openenergymonitor/STM32/Hardware/spice_models/current path1.png

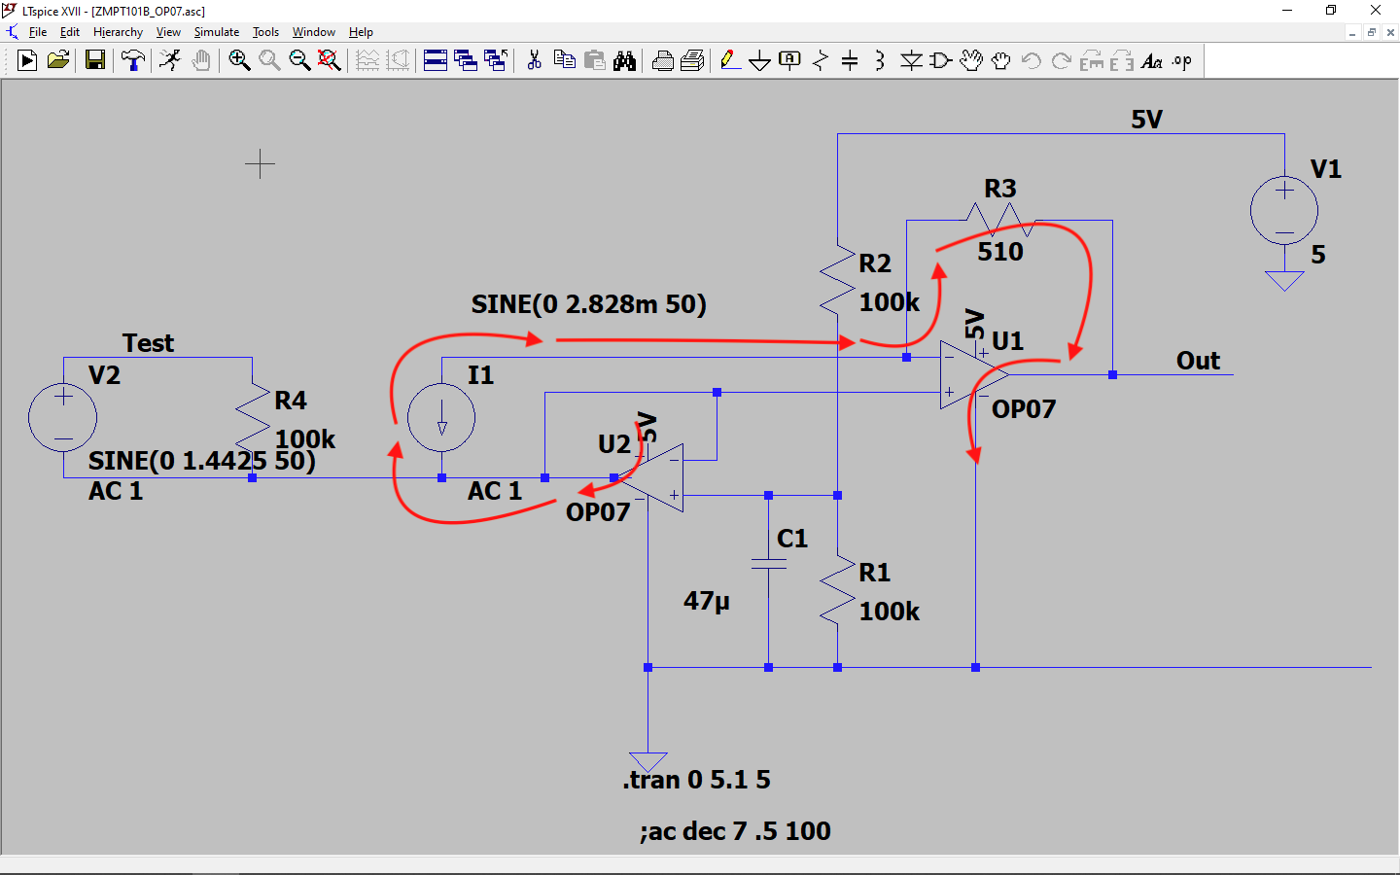
Hardware/spice_models/current path1.png
