openenergymonitor/STM32/Hardware/stm32-pi_basic/5/board.png

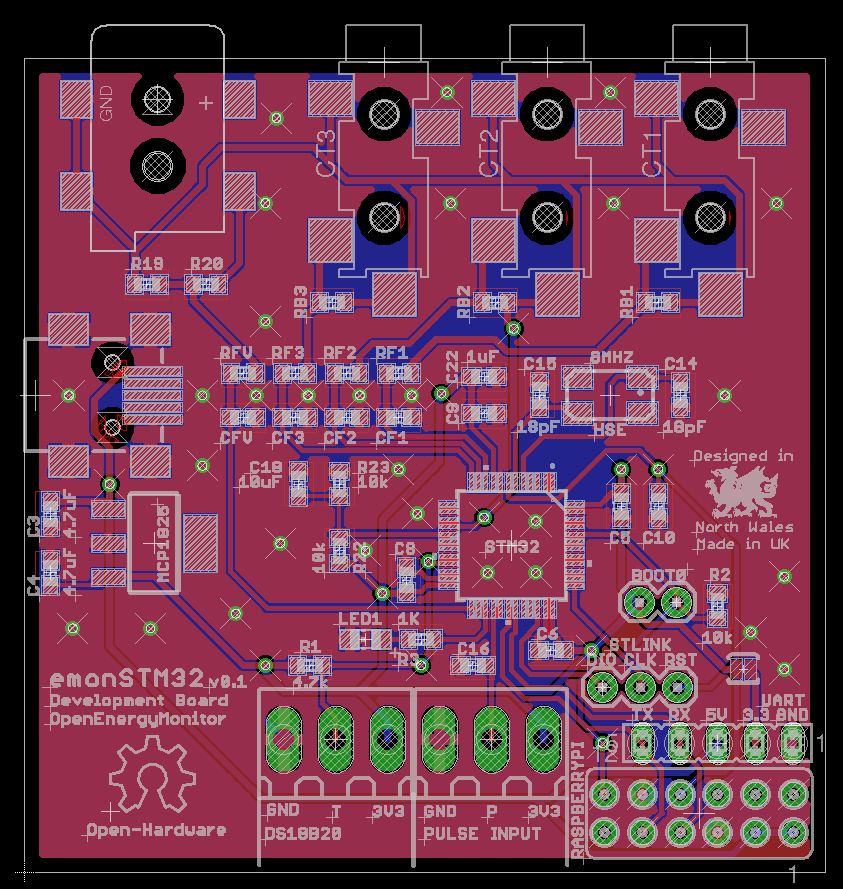
Hardware/stm32-pi_basic/5/board.png
