openenergymonitor/STM32/Hardware/stm32-pi_full/_datasheets/usw25w2a_04.jpg

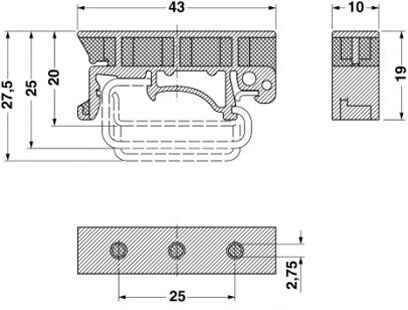
Hardware/stm32-pi_full/_datasheets/usw25w2a_04.jpg
