openenergymonitor/STM32/Hardware/stm32-pi_full/_datasheets/voltage stm32 watt hour meter.png

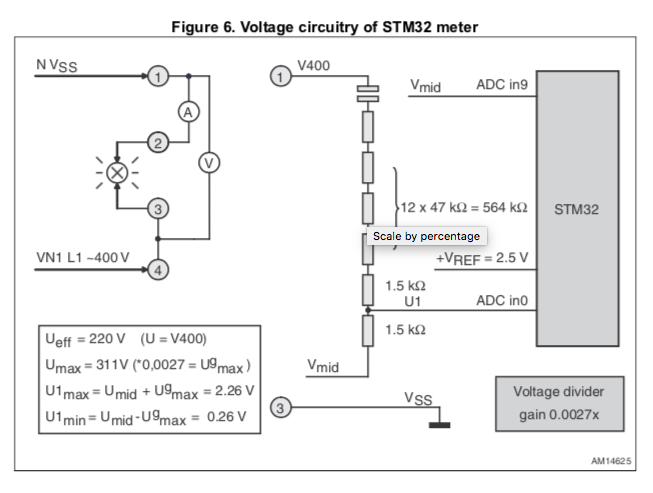
Hardware/stm32-pi_full/_datasheets/voltage stm32 watt hour meter.png
