openenergymonitor/STM32/Hardware/stm32-pi_full/_images/tp-link router.jpg

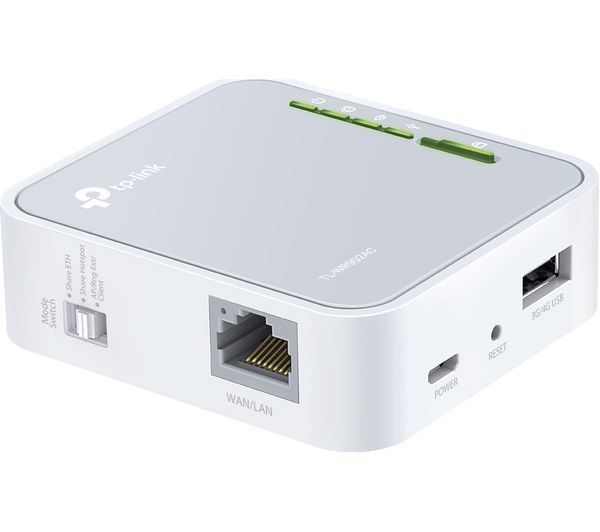
Hardware/stm32-pi_full/_images/tp-link router.jpg
