openenergymonitor/STM32/Hardware/stm32-pi_full/_images/v0.5/2019-07-29 11.01.41.jpg

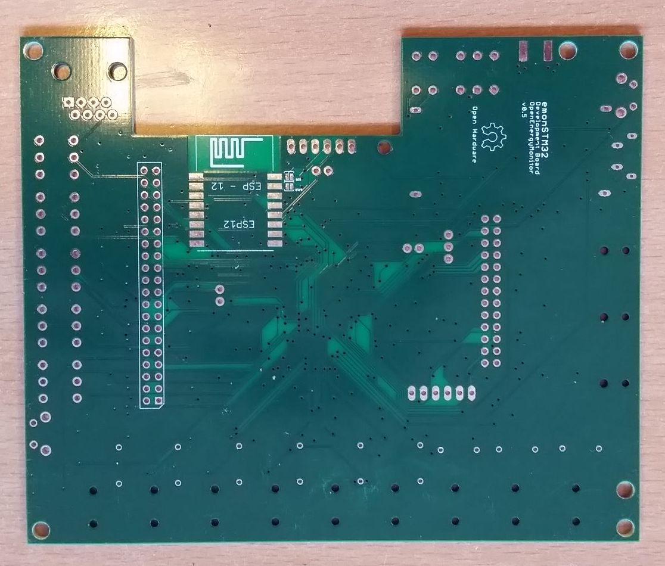
Hardware/stm32-pi_full/_images/v0.5/2019-07-29 11.01.41.jpg
