openenergymonitor/STM32/Hardware/stm32-pi_full/_images/v0.5/2019-08-09 16.36.07.jpg

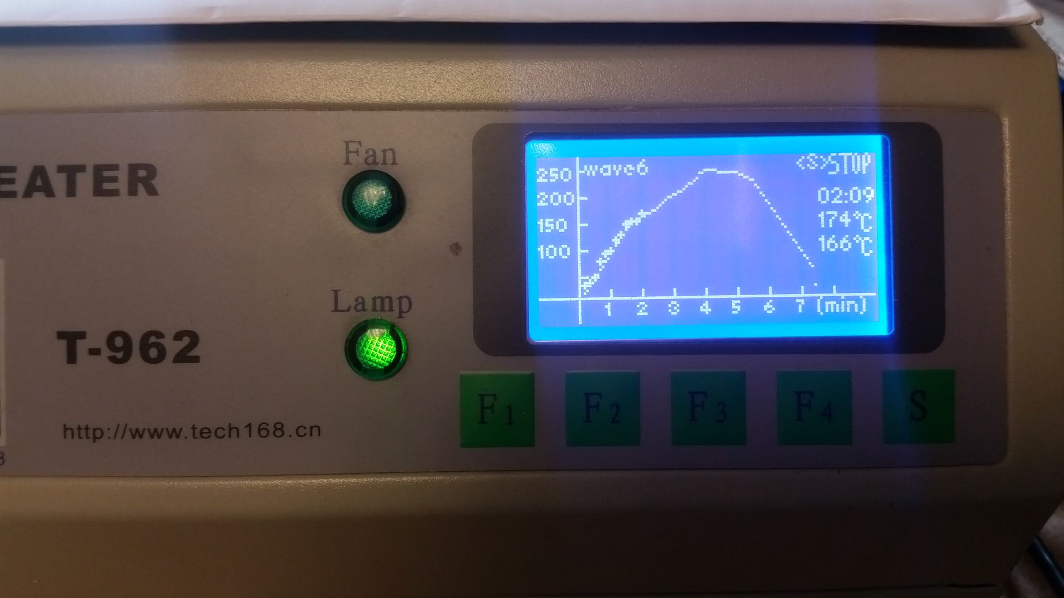
Hardware/stm32-pi_full/_images/v0.5/2019-08-09 16.36.07.jpg
