openenergymonitor/STM32/Hardware/stm32-pi_full/_images/v0.5/2019-08-09 17.46.59.jpg

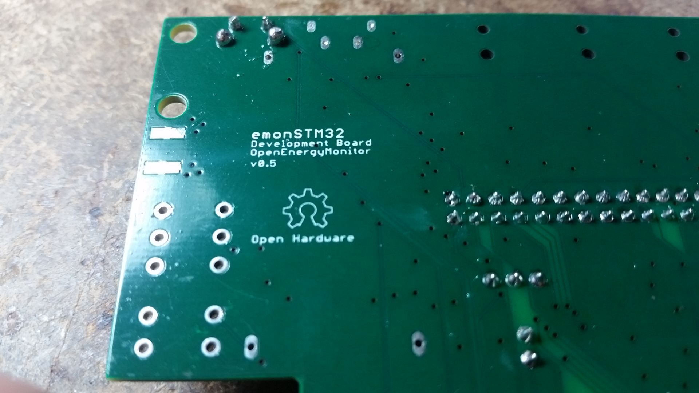
Hardware/stm32-pi_full/_images/v0.5/2019-08-09 17.46.59.jpg
