openenergymonitor/STM32/Hardware/stm32-pi_full/_images/v0.5/v0.5 2019-08-30 15.09.01.jpg

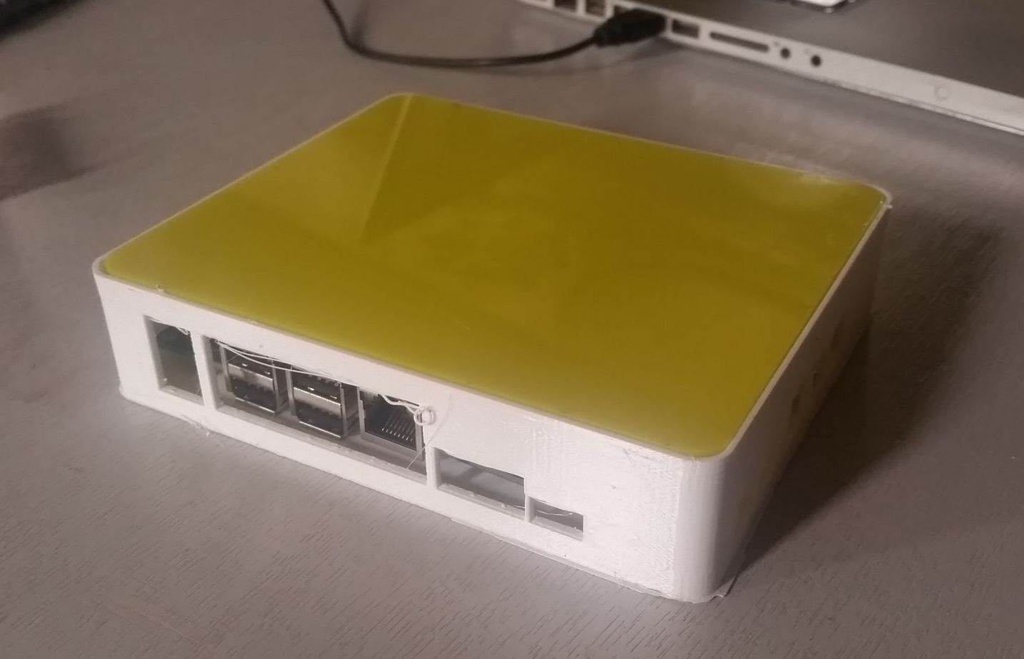
Hardware/stm32-pi_full/_images/v0.5/v0.5 2019-08-30 15.09.01.jpg
