openenergymonitor/STM32/Hardware/stm32-pi_full/_images/v0.6 Sept 2019/v0.6 top pcb.png

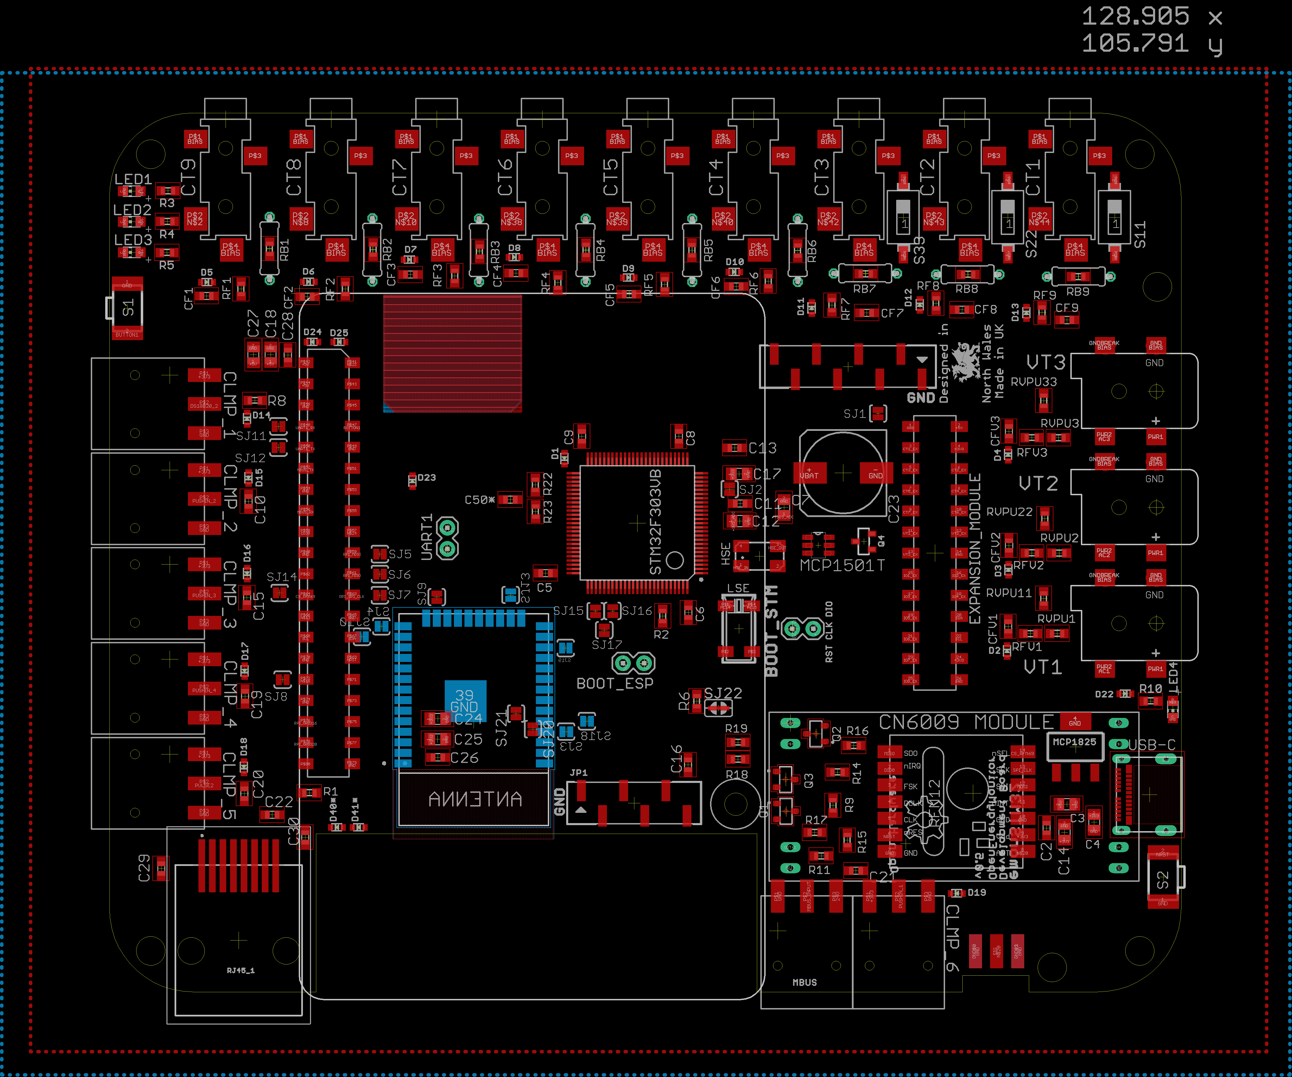
Hardware/stm32-pi_full/_images/v0.6 Sept 2019/v0.6 top pcb.png
