openenergymonitor/STM32/images/cad enclosure1.png

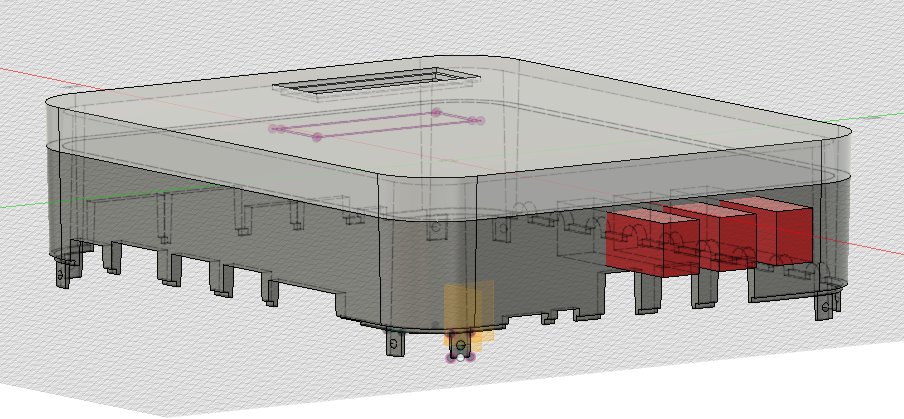
images/cad enclosure1.png
