openenergymonitor/STM32/images/emon3ct_pins.jpg

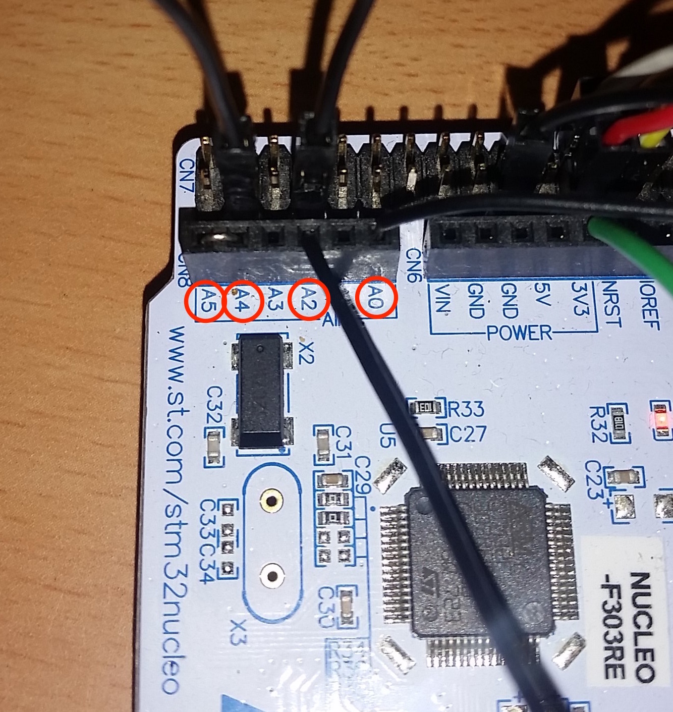
images/emon3ct_pins.jpg
