openenergymonitor/STM32/images/lowpassq.JPG

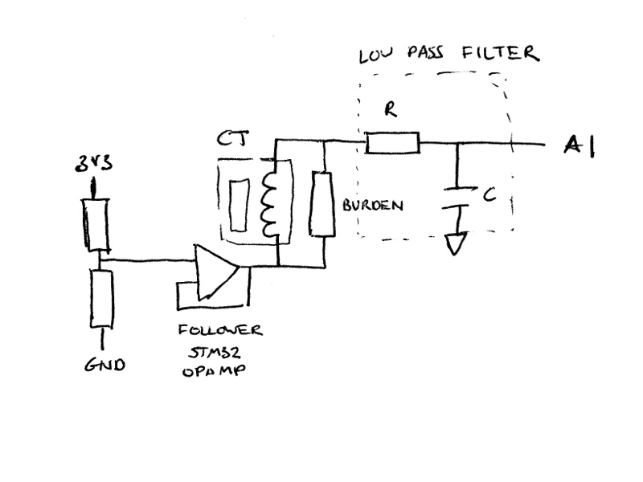
images/lowpassq.JPG
