openenergymonitor/STM32/images/stm32 orcad files to eaglecad/9.jpeg

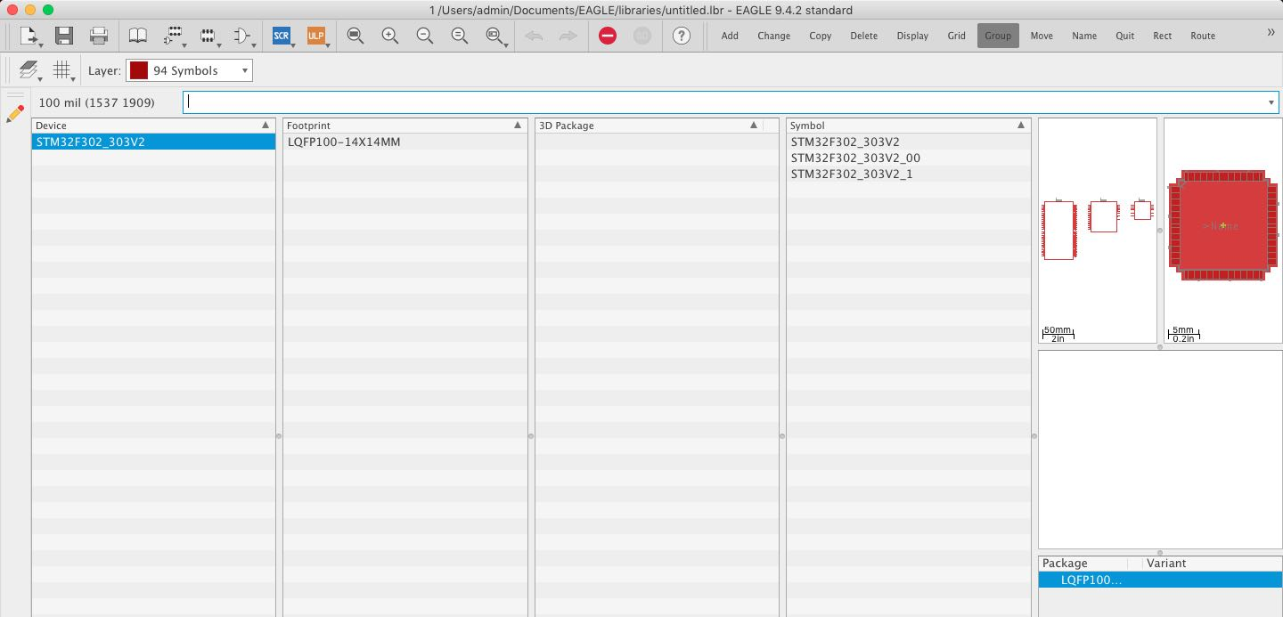
images/stm32 orcad files to eaglecad/9.jpeg
