openenergymonitor/STM32/images/stm32f303cb/stm32f303cbt6_uarts.png

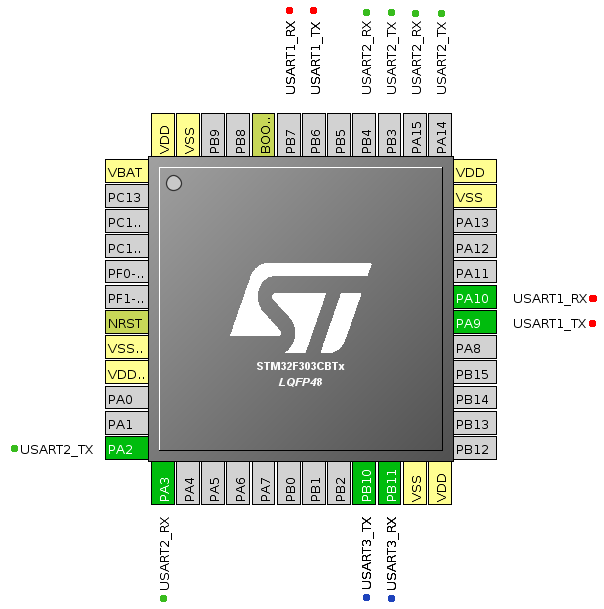
images/stm32f303cb/stm32f303cbt6_uarts.png
