openenergymonitor/STM32/images/TIM8.png

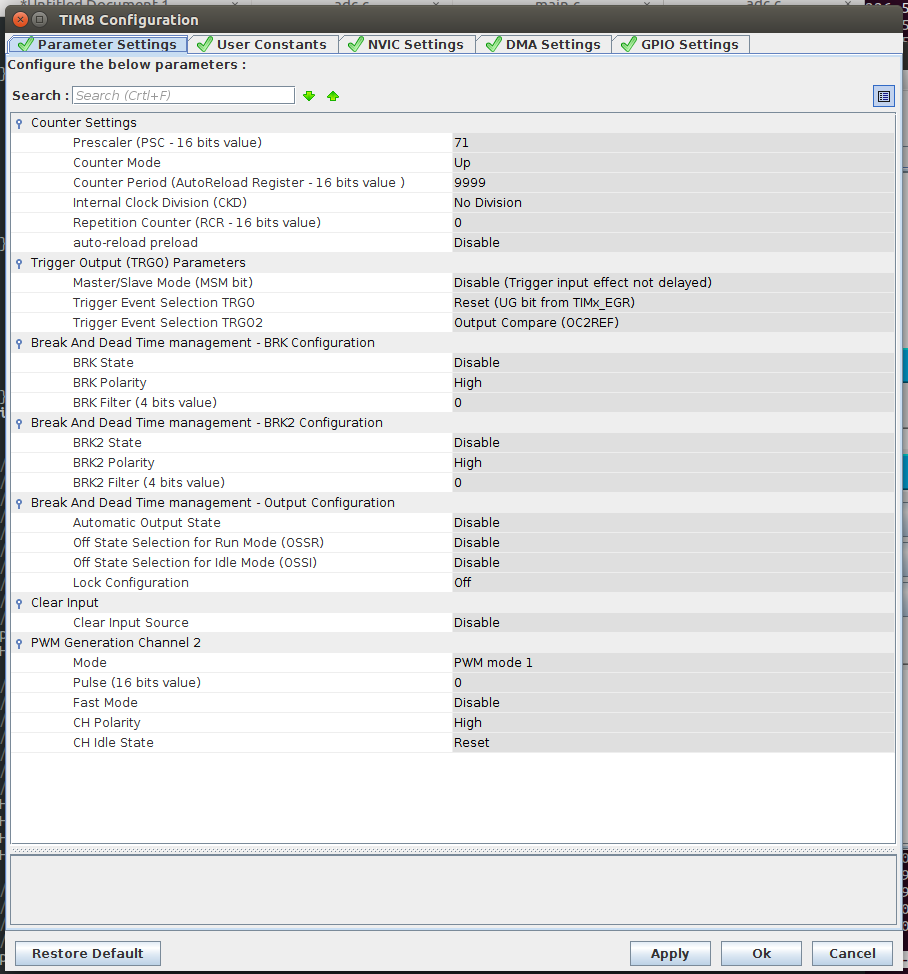
images/TIM8.png
