openenergymonitor/STM32/images/txshield_3.3V_mod.jpg

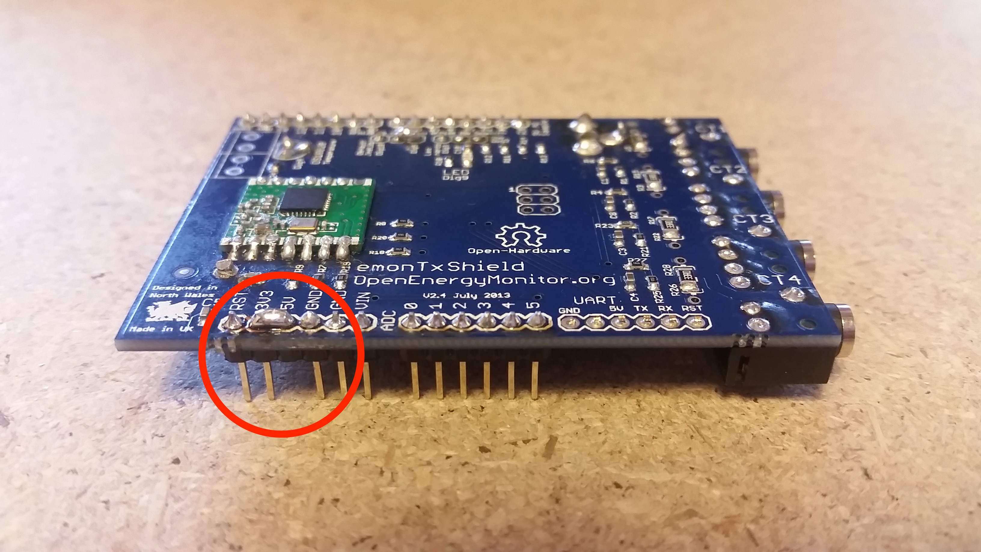
images/txshield_3.3V_mod.jpg
