openenergymonitor/STM32/images/v0.7 routing screeshots/cts vts gnd pwr.png

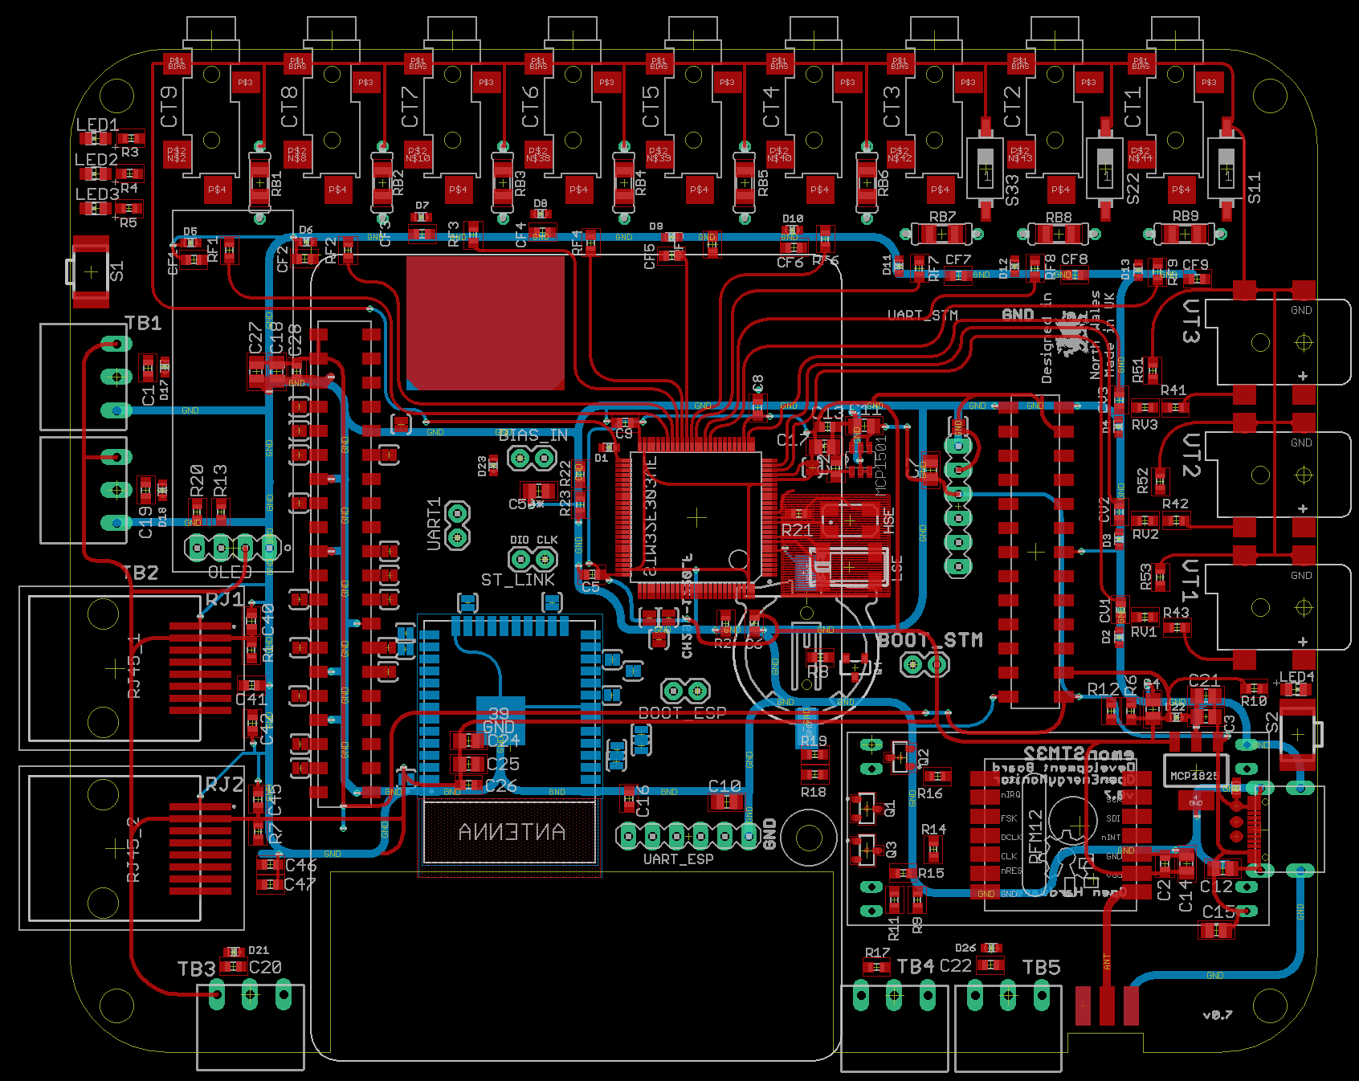
images/v0.7 routing screeshots/cts vts gnd pwr.png
