openenergymonitor/STM32/literature/3phase_amp_volt_nano.jpg

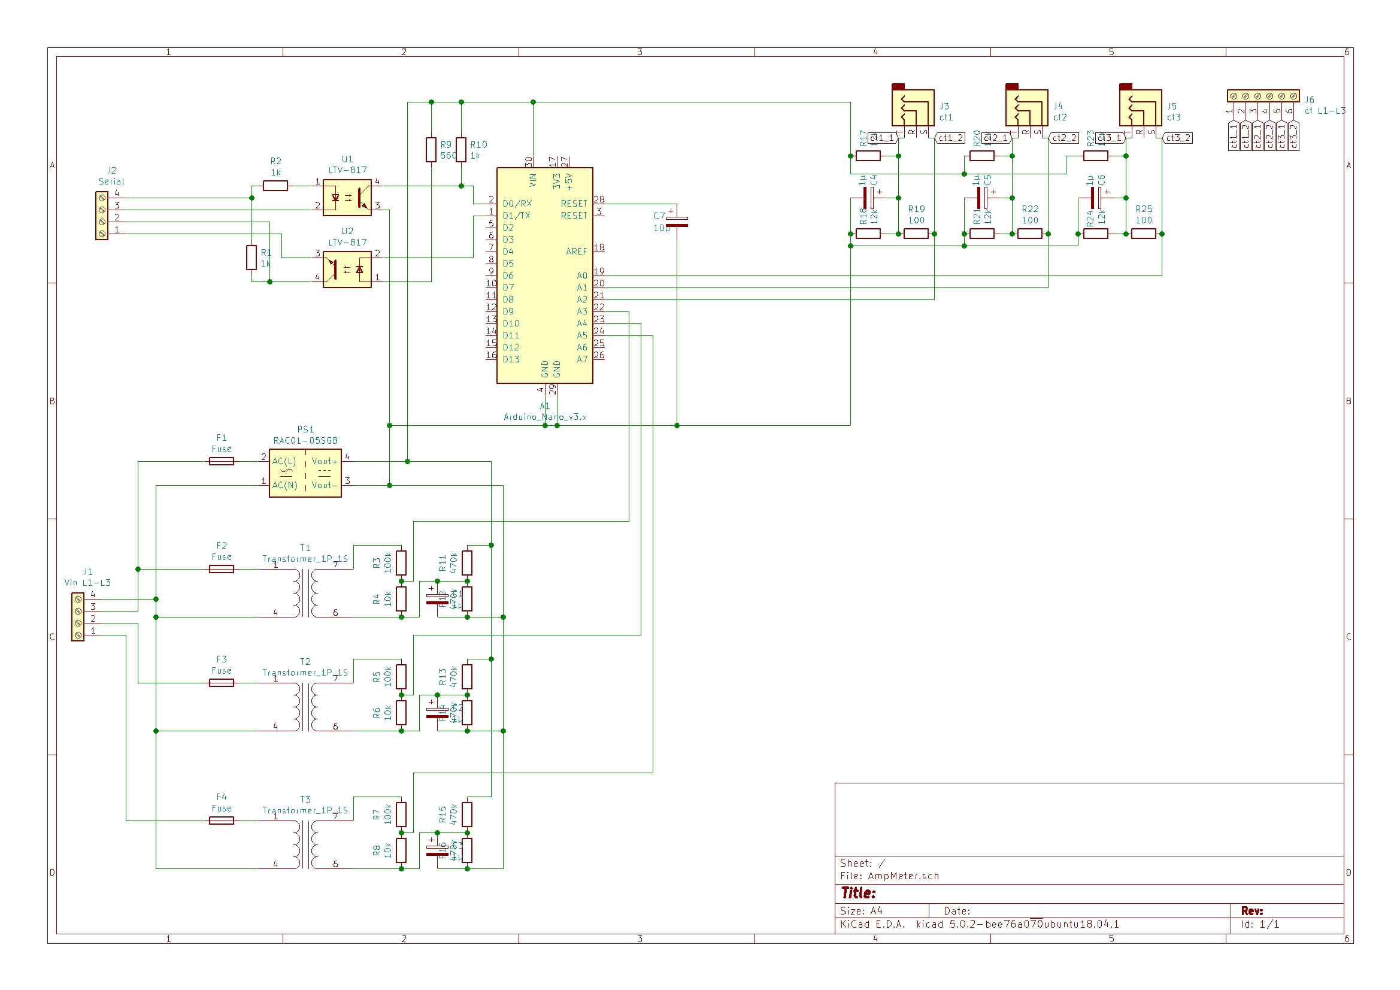
literature/3phase_amp_volt_nano.jpg
