openenergymonitor/STM32/Software/DAC_F303K8/3-phase generator/working1.jpg

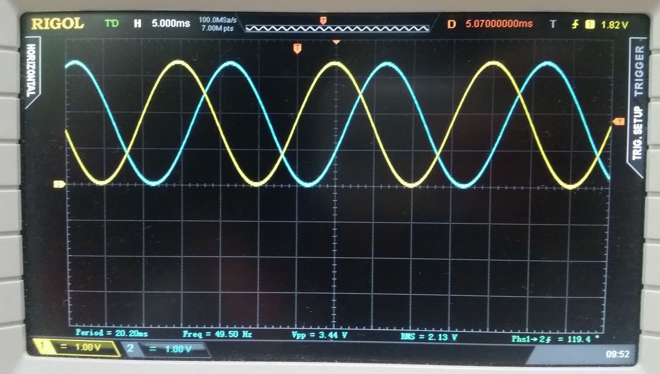
Software/DAC_F303K8/3-phase generator/working1.jpg
