openenergymonitor/STM32/Software/DAC_F303K8/3-phase generator/working2.jpg

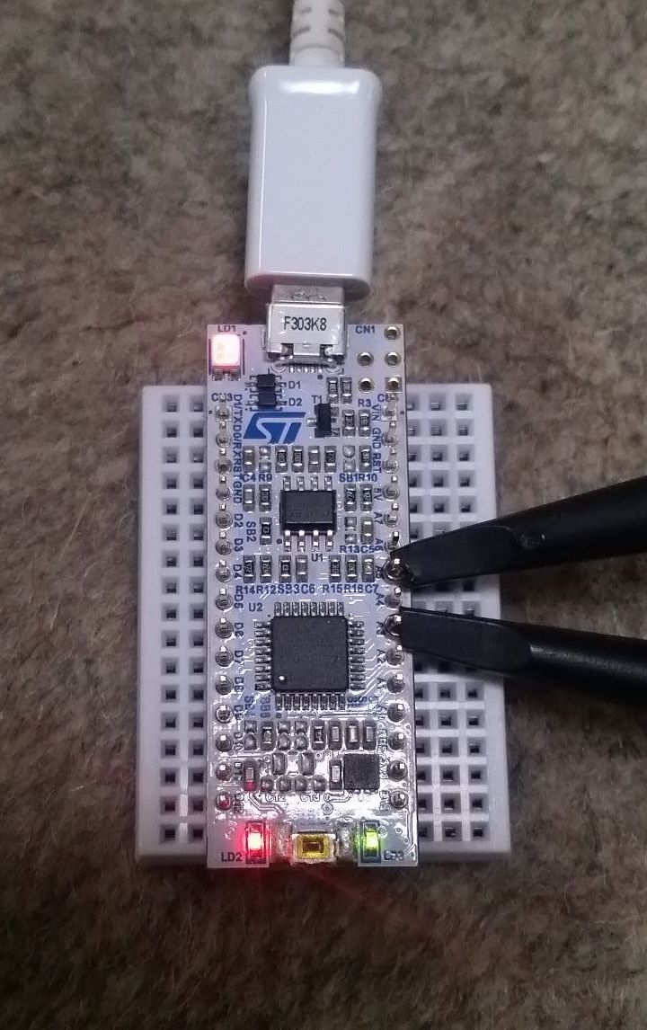
Software/DAC_F303K8/3-phase generator/working2.jpg
