openenergymonitor/STM32/Software/Emon3CT/fritzing diagram draft.png

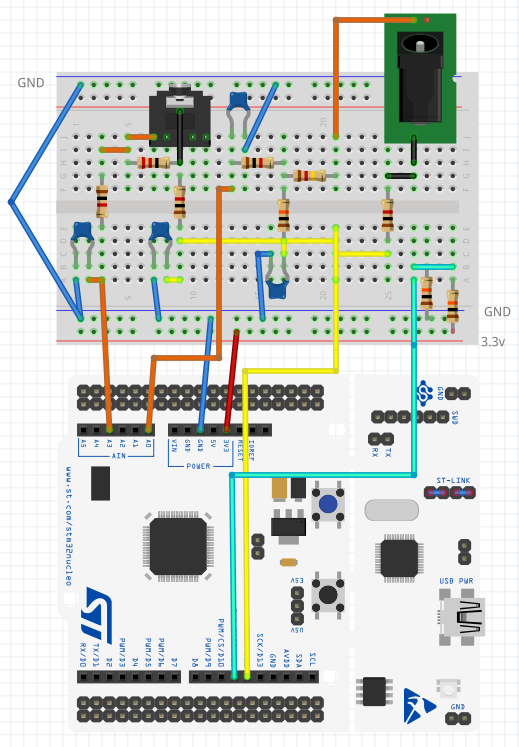
Software/Emon3CT/fritzing diagram draft.png
