openenergymonitor/STM32/images/rfm69_images/emon3ct_rfm69_wiring.jpg

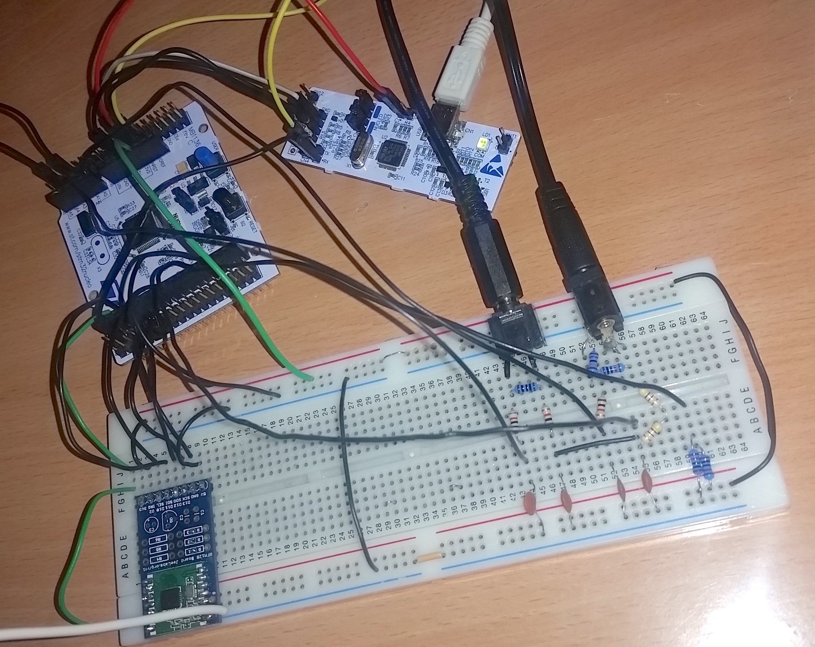
images/rfm69_images/emon3ct_rfm69_wiring.jpg
