openenergymonitor/STM32/docs/tests/1_diagram.png

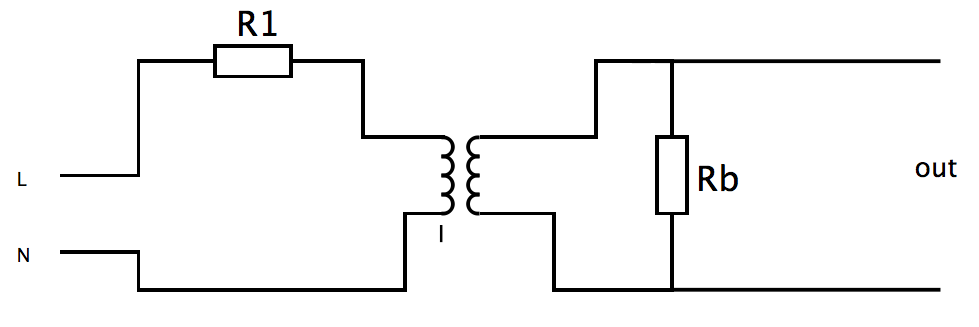
docs/tests/1_diagram.png
