openenergymonitor/STM32/docs/tests/u.i. test 29-9-2020.jpg

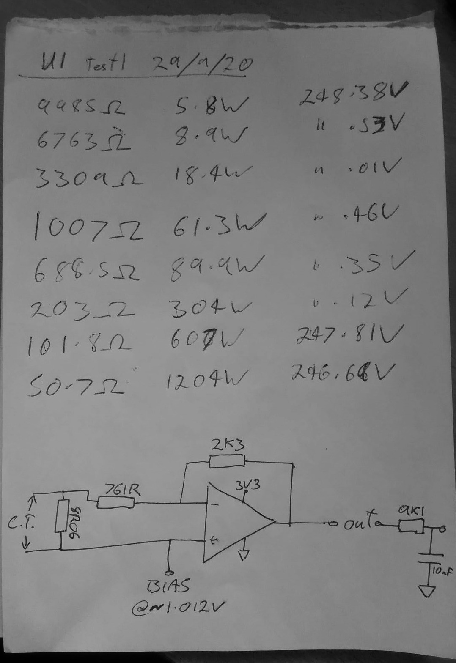
docs/tests/u.i. test 29-9-2020.jpg
