openenergymonitor/STM32/Hardware/stm32-pi_basic/4/stm32hw03.brd

## EAGLE design Hardware/stm32-pi_basic/4/stm32hw03.brd (2018-11-28)

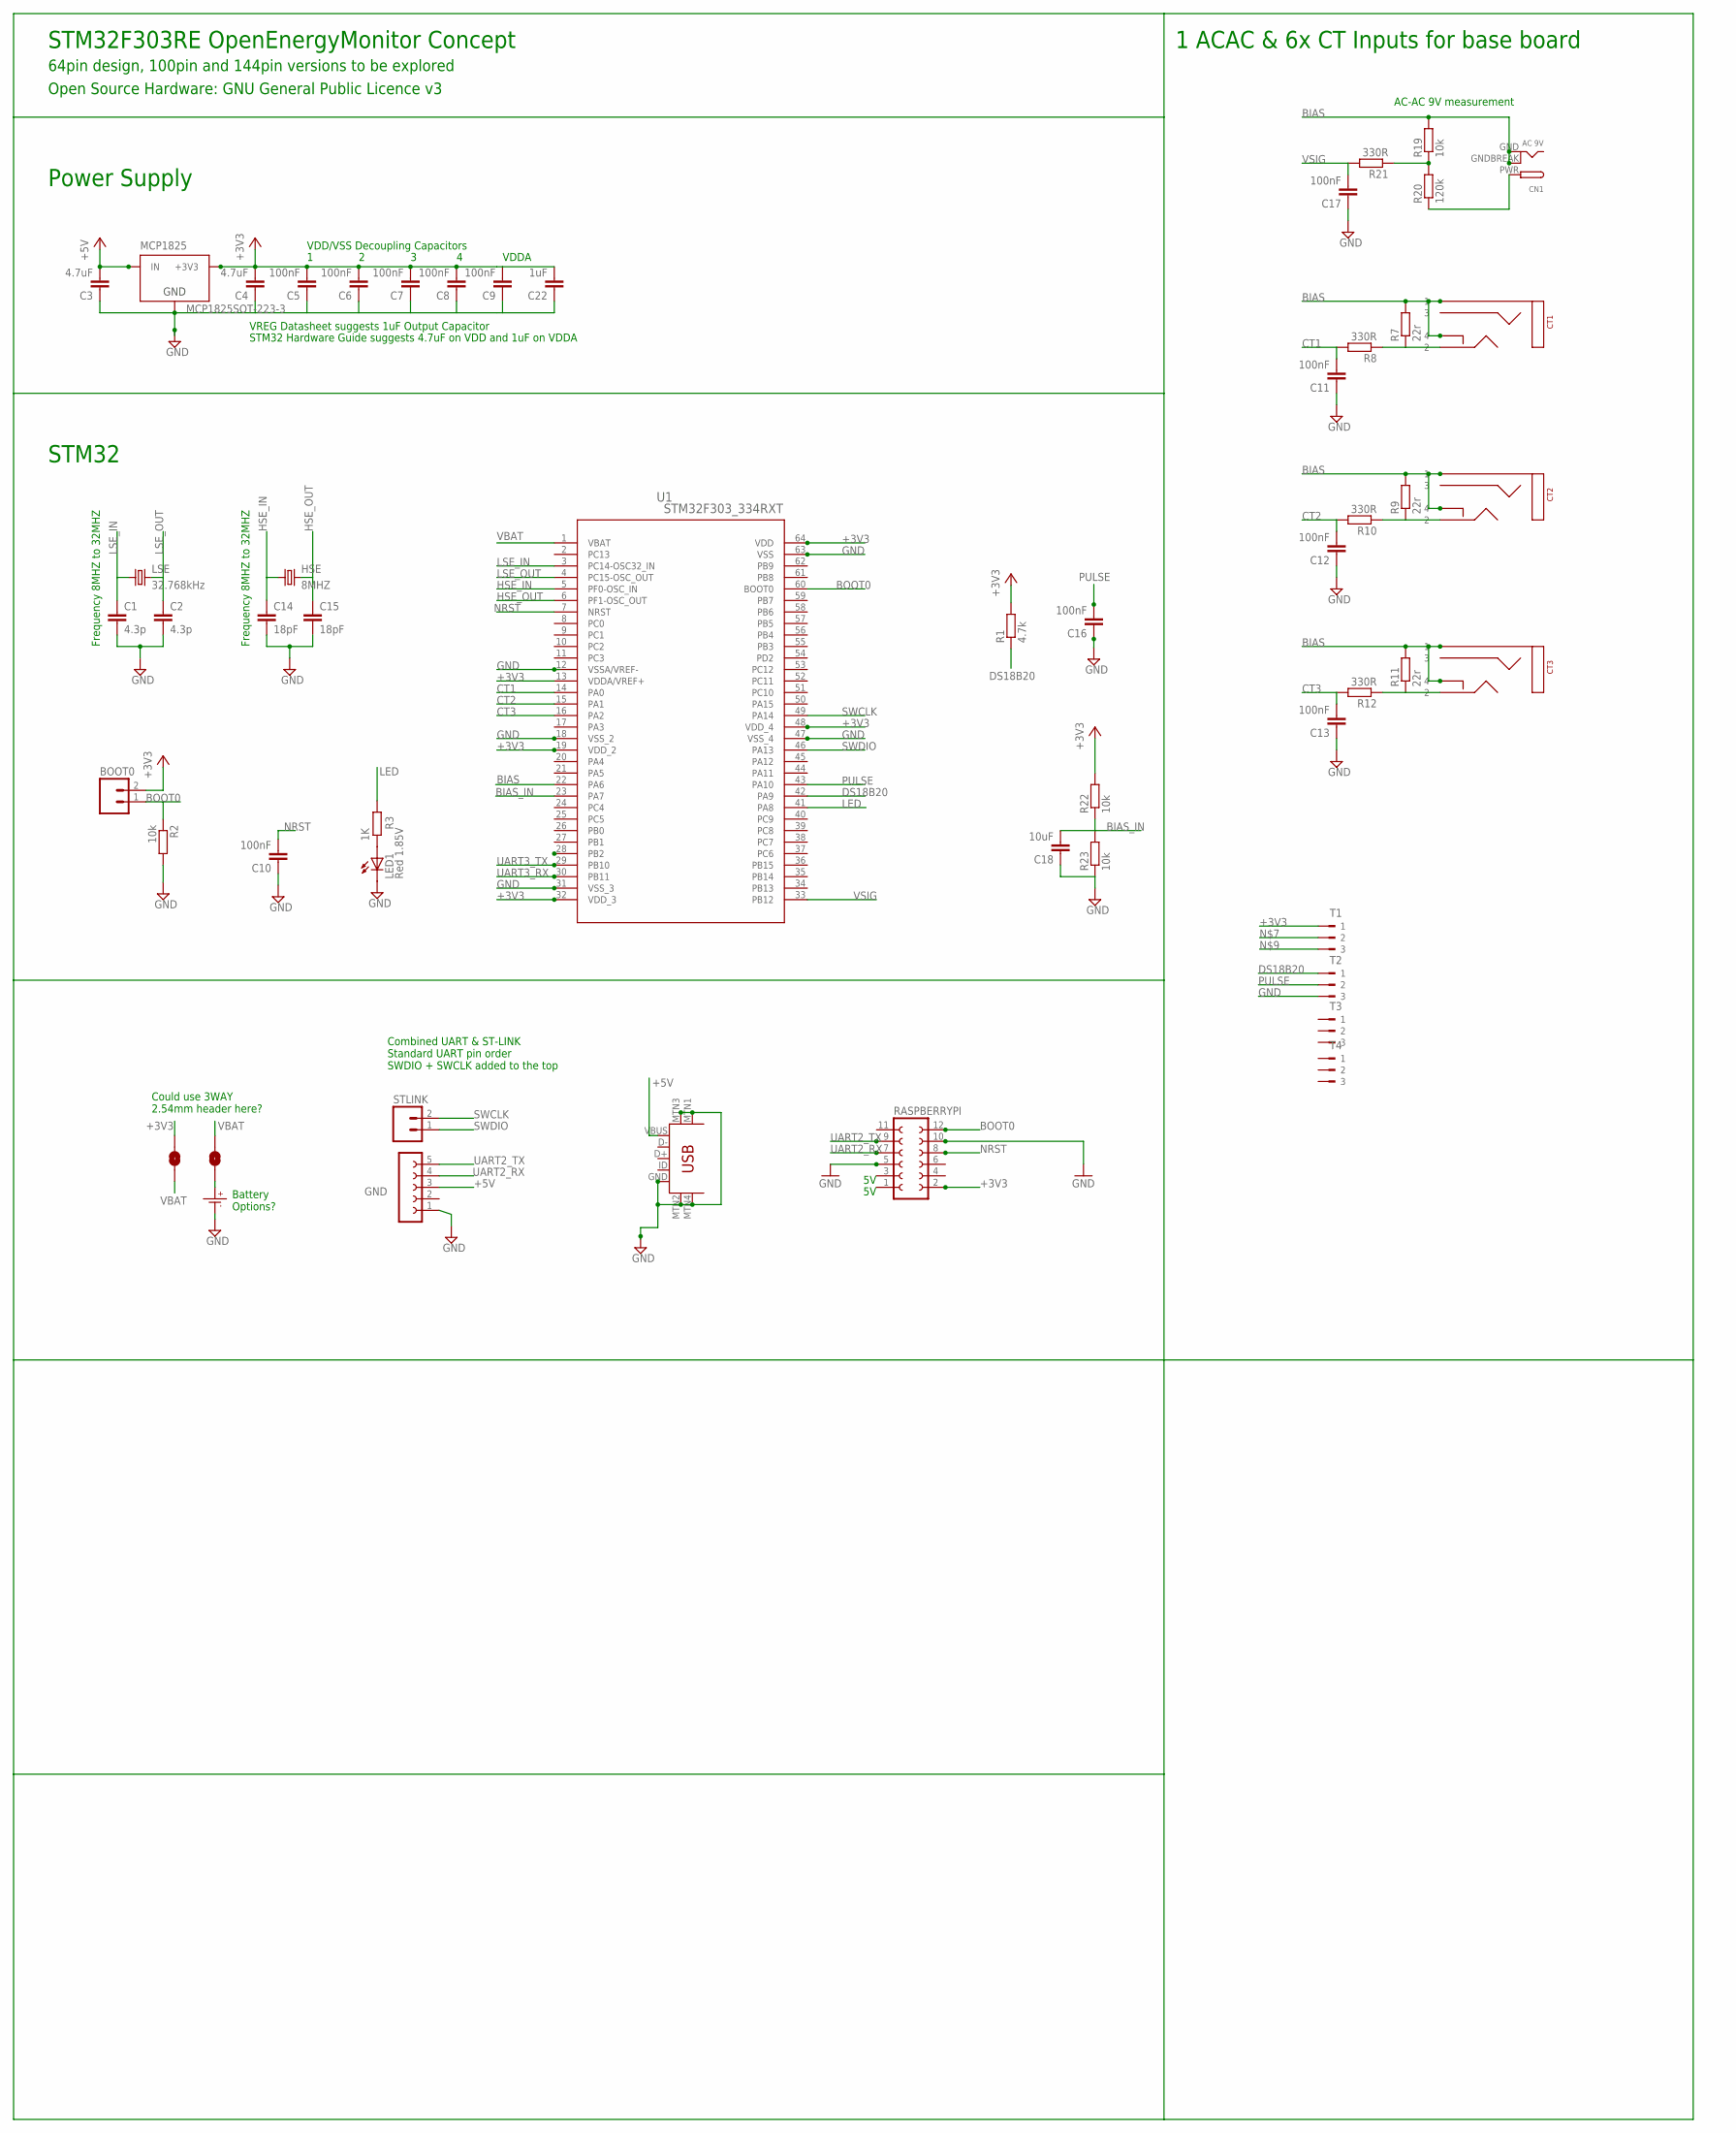
[picture p140: schematic stm32hw03.sch]

Parts:
3V3: SOLDERJUMPERNO; SJ_2S-NO
BATTERY: SOLDERJUMPERNO; SJ_2S-NO
BOOT0: M02PTH; 1X02
C1, C2: 4.3p; C0603
C3, C4: 4.7uF; C0603
C5, C6, C7, C8, C9, C10, C11, C12, C13, C16, C17: 100nF; C0603
C14, C15: 18pF; C0603
C18: 10uF; C0603
C22: 1uF; C0603
CN1: AC 9V; DCJACK_2MM_PTH
CR1220: CR1220SMD; MPN Harwin S8411-45R
CT1, CT2, CT3: STEREO_SMD; STEREO_SMT
GND: UART; FE05-1
HSE: 8MHZ; CTS406
LED1: Red 1.85V; CHIP-LED0805
LSE: 32.768kHz; MC-306
MCP1825: MCP1825SOT-223-3; SOT-223
R1: 4.7k; R0603
R2, R19, R22, R23: 10k; R0603
R3: 1K; R0603
R7, R9, R11: 22r; R0603
R8, R10, R12, R21: 330R; R0603
R20: 120k; R0603
RASPBERRYPI: FE06-2
STLINK: M02PTH; 1X02
T1, T2, T3, T4: 180-3
U1: STM32F303_334RXT; LQFP64-10X10MM
U$10: USB-MINIB-5PIN; USB-MINIB-CISECO

Connections:
+3V3: 3V3.1, BOOT0.2, C4.2, C5.2, C6.2, C7.2, C8.2, C9.2, C22.2, MCP1825.3 (+3V3), R1.2, R22.2, RASPBERRYPI.2, T1.1, U1.13 (VDDA/VREF+), U1.19 (VDD_2), U1.32 (VDD_3), U1.48 (VDD_4), U1.64 (VDD)
+5V: C3.2, GND.3, MCP1825.1 (IN), U$10.VBUS
AC: CN1.PWR, R20.1
ADC0: R19.1, R20.2, R21.1
BIAS: CN1.GND, CN1.GNDBREAK, CT1.P$1 (1), CT1.P$4 (4), CT2.P$1 (1), CT2.P$4 (4), CT3.P$1 (1), CT3.P$4 (4), R7.2, R9.2, R11.2, R19.2, U1.22 (PA6)
BIAS_IN: C18.2, R22.1, R23.2, U1.23 (PA7)
BOOT0: BOOT0.1, R2.1, RASPBERRYPI.12, U1.60 (BOOT0)
CT1: C11.2, R8.2, U1.14 (PA0)
CT2: C12.2, R10.2, U1.15 (PA1)
CT3: C13.2, R12.2, U1.16 (PA2)
DS18B20: R1.1, T2.1, U1.42 (PA9)
GND: C1.2, C2.2, C3.1, C4.1, C5.1, C6.1, C7.1, C8.1, C9.1, C10.1, C11.1, C12.1, C13.1, C14.2, C15.2, C16.1, C17.1, C18.1, C22.1, CR1220.P- (P$-), GND.1, LED1.C, MCP1825.2 (GND), R2.2, R23.1, RASPBERRYPI.5, RASPBERRYPI.10, T2.3, U1.12 (VSSA/VREF-), U1.18 (VSS_2), U1.31 (VSS_3), U1.47 (VSS_4), U1.63 (VSS), U$10.GND, U$10.MTN1 (MTN2), U$10.MTN2 (MTN3), U$10.MTN3 (MTN1), U$10.MTN4
HSE_IN: C14.1, HSE.1, U1.5 (PF0-OSC_IN)
HSE_OUT: C15.1, HSE.3 (2), U1.6 (PF1-OSC_OUT)
LED: R3.2, U1.41 (PA8)
LSE_IN: C1.1, LSE.1, U1.3 (PC14-OSC32_IN)
LSE_OUT: C2.1, LSE.4 (2), U1.4 (PC15-OSC_OUT)
unnamed: BATTERY.2, CR1220.P+ (P$+)
unnamed: CT1.P$2 (2), R7.1, R8.1
unnamed: CT2.P$2 (2), R9.1, R10.1
unnamed: CT3.P$2 (2), R11.1, R12.1
unnamed: LED1.A, R3.1
NRST: C10.2, RASPBERRYPI.8, U1.7 (NRST)
PULSE: C16.2, T2.2, U1.43 (PA10)
SWCLK: STLINK.2, U1.49 (PA14)
SWDIO: STLINK.1, U1.46 (PA13)
UART2_RX: GND.4, RASPBERRYPI.7
UART2_TX: GND.5, RASPBERRYPI.9
UART3_RX: U1.30 (PB11)
UART3_TX: U1.29 (PB10)
VBAT: 3V3.2, BATTERY.1, U1.1 (VBAT)
VSIG: C17.2, R21.2, U1.33 (PB12)

Notes on the sheet:
VDD/VSS Decoupling Capacitors
VDDA
VREG Datasheet suggests 1uF Output Capacitor
STM32 Hardware Guide suggests 4.7uF on VDD and 1uF on VDDA
Frequency 8MHZ to 32MHZ
Could use 3WAY 2.54mm header here?
Battery Options?
Combined UART & ST-LINK Standard UART pin order SWDIO + SWCLK added to the top
AC-AC 9V measurement
1 ACAC & 6x CT Inputs for base board
STM32F303RE OpenEnergyMonitor Concept
64pin design, 100pin and 144pin versions to be explored
Power Supply
STM32
Open Source Hardware: GNU General Public Licence v3
