openenergymonitor/STM32/Hardware/stm32-pi_basic/4/stm32hw03.brd

## EAGLE design Hardware/stm32-pi_basic/4/stm32hw03.brd (continued)

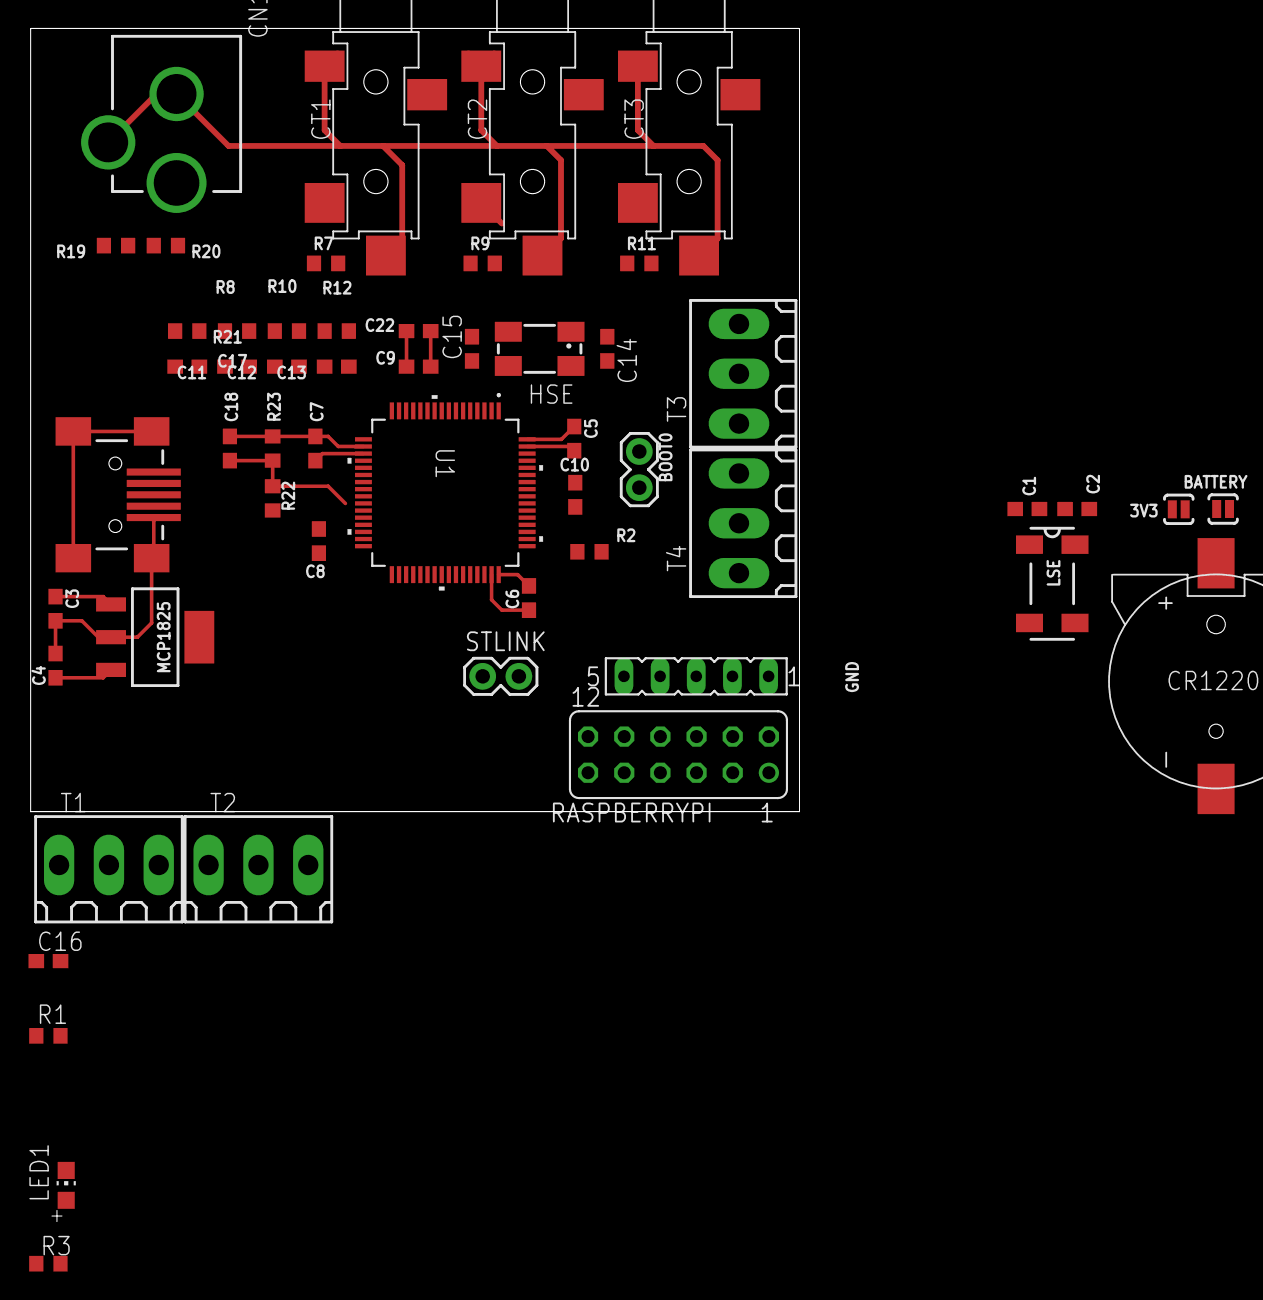
[picture p141: board Hardware/stm32-pi_basic/4/stm32hw03.brd from above]

Board: 2 copper layers, 54.0 x 55.0 mm, 54 parts (0 on the bottom side), 30 nets.
