openenergymonitor/STM32/Software/Emon3CT_VET/Emon3CT_VET.ioc

Mcu.UserName=STM32F303VETx
PA0.Signal=ADC1_IN1
PA10.Signal=USART1_RX
PA9.Signal=USART1_TX
PB0.Signal=ADC3_IN12
PB1.Signal=ADC3_IN1
PB12.Signal=OPAMP4_VOUT
PC7.Signal=S_TIM8_CH2
PD10.Signal=GPIO_Output
PD11.Signal=OPAMP4_VINP
PD8.Signal=GPIO_Output
PD9.Signal=GPIO_Output
PE7.Signal=ADC3_IN13
PF0-OSC_IN.Signal=RCC_OSC_IN
PF1-OSC_OUT.Signal=RCC_OSC_OUT
