openenergymonitor/STM32/Software/RFM69/Src/RFM69.c

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
// Licence can be viewed at
// http://www.gnu.org/licenses/gpl-3.0.txt
//
// Please maintain this license information along with authorship
// and copyright notices in any redistribution of this code
// **********************************************************************************
#include <RFM69.h>
#include <RFM69registers.h>
#include <RFM69_ext.h>


char log_buffer[150];
uint8_t data[RF69_MAX_DATA_LEN]; // recv/xmit buf, including header & crc bytes
#define RFM69_DATA(x) data[x] // function to grab specific bytes from data[]
uint8_t datalen;
uint8_t senderID;
uint8_t targetID;                // should match _address
uint8_t payloadLen;
uint8_t ACK_Requested;
uint8_t ACK_RECEIVED;           // should be polled immediately after sending a packet with ACK request
uint8_t _mode;
int16_t rssi;                   // most accurate RSSI during reception (closest to the reception)

uint8_t _address;
uint8_t _powerLevel = 16; // 31 max
bool _promiscuousMode = false;
uint8_t _mode = RF69_MODE_STANDBY;




bool RFM69_initialize(uint16_t freqBand, uint8_t nodeID, uint16_t networkID)
{
  const uint8_t CONFIG[][2] =
  {
    /* 0x01 */ { REG_OPMODE, RF_OPMODE_SEQUENCER_ON | RF_OPMODE_LISTEN_OFF | RF_OPMODE_STANDBY },
    /* 0x02 */ { REG_DATAMODUL, RF_DATAMODUL_DATAMODE_PACKET | RF_DATAMODUL_MODULATIONTYPE_FSK | RF_DATAMODUL_MODULATIONSHAPING_00 }, // no shaping
    /* 0x03 */ { REG_BITRATEMSB, RF_BITRATEMSB_55555}, // default: 4.8 KBPS
    /* 0x04 */ { REG_BITRATELSB, RF_BITRATELSB_55555},
    /* 0x05 */ { REG_FDEVMSB, RF_FDEVMSB_50000}, // default: 5KHz, (FDEV + BitRate / 2 <= 500KHz)
    /* 0x06 */ { REG_FDEVLSB, RF_FDEVLSB_50000},

    /* 0x07 */ { REG_FRFMSB, (freqBand == RF69_315MHZ ? RF_FRFMSB_315 : (freqBand == RF69_433MHZ ? RF_FRFMSB_433 : (freqBand == RF69_868MHZ ? RF_FRFMSB_868 : RF_FRFMSB_915))) },
    /* 0x08 */ { REG_FRFMID, (freqBand == RF69_315MHZ ? RF_FRFMID_315 : (freqBand == RF69_433MHZ ? RF_FRFMID_433 : (freqBand == RF69_868MHZ ? RF_FRFMID_868 : RF_FRFMID_915))) },
    /* 0x09 */ { REG_FRFLSB, (freqBand == RF69_315MHZ ? RF_FRFLSB_315 : (freqBand == RF69_433MHZ ? RF_FRFLSB_433 : (freqBand == RF69_868MHZ ? RF_FRFLSB_868 : RF_FRFLSB_915))) },
    //* 0x07 */ { REG_FRFMSB, RF_FRFMSB_433 },
    //* 0x08 */ { REG_FRFMID, RF_FRFMID_433 },
    //* 0x09 */ { REG_FRFLSB, RF_FRFLSB_433 },
    /*
    // available frequency bands
    #define RF69_315MHZ            315 // non trivial values to avoid misconfiguration
    #define RF69_433MHZ            433
    #define RF69_868MHZ            868
    #define RF69_915MHZ            915
    */

    // looks like PA1 and PA2 are not implemented on RFM69W, hence the max output power is 13dBm
    // +17dBm and +20dBm are possible on RFM69HW
    // +13dBm formula: Pout = -18 + OutputPower (with PA0 or PA1**)
    // +17dBm formula: Pout = -14 + OutputPower (with PA1 and PA2)**
    // +20dBm formula: Pout = -11 + OutputPower (with PA1 and PA2)** and high power PA settings (section 3.3.7 in datasheet)
    ///* 0x11 */ { REG_PALEVEL, RF_PALEVEL_PA0_ON | RF_PALEVEL_PA1_OFF | RF_PALEVEL_PA2_OFF | RF_PALEVEL_OUTPUTPOWER_11111},
    ///* 0x13 */ { REG_OCP, RF_OCP_ON | RF_OCP_TRIM_95 }, // over current protection (default is 95mA)

    // RXBW defaults are { REG_RXBW, RF_RXBW_DCCFREQ_010 | RF_RXBW_MANT_24 | RF_RXBW_EXP_5} (RxBw: 10.4KHz)
    /* 0x19 */ { REG_RXBW, RF_RXBW_DCCFREQ_010 | RF_RXBW_MANT_16 | RF_RXBW_EXP_2 }, // (BitRate < 2 * RxBw)
    //for BR-19200: /* 0x19 */ { REG_RXBW, RF_RXBW_DCCFREQ_010 | RF_RXBW_MANT_24 | RF_RXBW_EXP_3 },
    /* 0x25 */ { REG_DIOMAPPING1, RF_DIOMAPPING1_DIO0_01 }, // DIO0 is the only IRQ we're using
    /* 0x26 */ { REG_DIOMAPPING2, RF_DIOMAPPING2_CLKOUT_OFF }, // DIO5 ClkOut disable for power saving
    /* 0x28 */ { REG_IRQFLAGS2, RF_IRQFLAGS2_FIFONOTEMPTY }, // writing to this bit ensures that the FIFO & status flags are reset
    /* 0x29 */ { REG_RSSITHRESH, 220 }, // must be set to dBm = (-Sensitivity / 2), default is 0xE4 = 228 so -114dBm
    ///* 0x2D */ { REG_PREAMBLELSB, RF_PREAMBLESIZE_LSB_VALUE } // default 3 preamble bytes 0xAAAAAA
    /* 0x2E */ { REG_SYNCCONFIG, RF_SYNC_ON | RF_SYNC_FIFOFILL_AUTO | RF_SYNC_SIZE_2 | RF_SYNC_TOL_0 },
    ///* 0x2F */ { REG_SYNCVALUE1, (uint8_t)(networkID & 0x00FF) },  // NETWORK ID lower 8 bits
    ///* 0x30 */ { REG_SYNCVALUE2, (uint8_t)(networkID >> 8) },      // NETWORK ID higher 8 bits
    /* 0x2F */ { REG_SYNCVALUE1, 0x2D },      // attempt to make this compatible with sync1 byte of RFM12B lib
    /* 0x30 */ { REG_SYNCVALUE2, networkID }, // NETWORK ID
    /* 0x37 */ { REG_PACKETCONFIG1, RF_PACKET1_FORMAT_VARIABLE | RF_PACKET1_DCFREE_OFF | RF_PACKET1_CRC_ON | RF_PACKET1_CRCAUTOCLEAR_ON | RF_PACKET1_ADRSFILTERING_OFF },
    /* 0x38 */ { REG_PAYLOADLENGTH, 66 }, // in variable length mode: the max frame size, not used in TX
    ///* 0x39 */ { REG_NODEADRS, nodeID }, // turned off because we're not using address filtering
    /* 0x3C */ { REG_FIFOTHRESH, RF_FIFOTHRESH_TXSTART_FIFONOTEMPTY | RF_FIFOTHRESH_VALUE }, // TX on FIFO not empty
    /* 0x3D */ { REG_PACKETCONFIG2, RF_PACKET2_RXRESTARTDELAY_2BITS | RF_PACKET2_AUTORXRESTART_ON | RF_PACKET2_AES_OFF }, // RXRESTARTDELAY must match transmitter PA ramp-down time (bitrate dependent)
    //for BR-19200: /* 0x3D */ { REG_PACKETCONFIG2, RF_PACKET2_RXRESTARTDELAY_NONE | RF_PACKET2_AUTORXRESTART_ON | RF_PACKET2_AES_OFF }, // RXRESTARTDELAY must match transmitter PA ramp-down time (bitrate dependent)
    /* 0x6F */ { REG_TESTDAGC, RF_DAGC_IMPROVED_LOWBETA0 }, // run DAGC continuously in RX mode for Fading Margin Improvement, recommended default for AfcLowBetaOn=0
    {255, 0}
  };
  uint8_t i;

  RFM69_SetCSPin(1);

  for (i = 0; CONFIG[i][0] != 255; i++) {
    RFM69_writeReg(CONFIG[i][0], CONFIG[i][1]);
  }

  // check written registers
  for (i = 0; CONFIG[i][0] != 255; i++) {
    if(CONFIG[i][0] != REG_IRQFLAGS2)
    {
      if(RFM69_readReg(CONFIG[i][0]) != CONFIG[i][1]) {
        return false;
      }
    }
  }

  // Encryption is persistent between resets and can trip you up during debugging.
  // Disable it during initialization so we always start from a known state.
  RFM69_encrypt(0);

  RFM69_setHighPower(); // called regardless if it's a RFM69W or RFM69HW
  RFM69_setMode(RF69_MODE_STANDBY);
  Timeout_SetTimeout1(50);
  while (((RFM69_readReg(REG_IRQFLAGS1) & RF_IRQFLAGS1_MODEREADY) == 0x00) && !Timeout_IsTimeout1()); // wait for ModeReady
  if (Timeout_IsTimeout1())
  {
    return false;
  }

  _address = nodeID;
  return true;
}


// internal
static void RFM69_sendFrame(uint8_t toAddress, const void* buffer, uint8_t size, bool requestACK, bool sendACK);

// return the frequency (in Hz)
uint32_t RFM69_getFrequency()
{
  return RF69_FSTEP * (((uint32_t) RFM69_readReg(REG_FRFMSB) << 16) + ((uint16_t) RFM69_readReg(REG_FRFMID) << 8) + RFM69_readReg(REG_FRFLSB));
}

// set the frequency (in Hz)
void RFM69_setFrequency(uint32_t freqHz)
{
  uint8_t oldMode = _mode;
  if (oldMode == RF69_MODE_TX) {
    RFM69_setMode(RF69_MODE_RX);
  }
  freqHz /= RF69_FSTEP; // divide down by FSTEP to get FRF
  RFM69_writeReg(REG_FRFMSB, freqHz >> 16);
  RFM69_writeReg(REG_FRFMID, freqHz >> 8);
  RFM69_writeReg(REG_FRFLSB, freqHz);
  if (oldMode == RF69_MODE_RX) {
    RFM69_setMode(RF69_MODE_SYNTH);
  }
  RFM69_setMode(oldMode);
}

void RFM69_setMode(uint8_t newMode)
{
  if (newMode == _mode)
    return;

  switch (newMode) {
    case RF69_MODE_TX:
      RFM69_writeReg(REG_OPMODE, (RFM69_readReg(REG_OPMODE) & 0xE3) | RF_OPMODE_TRANSMITTER);
      if (ISRFM69HW) RFM69_setHighPowerRegs(true);
      break;
    case RF69_MODE_RX:
      RFM69_writeReg(REG_OPMODE, (RFM69_readReg(REG_OPMODE) & 0xE3) | RF_OPMODE_RECEIVER);
      if (ISRFM69HW) RFM69_setHighPowerRegs(false);
      break;
    case RF69_MODE_SYNTH:
      RFM69_writeReg(REG_OPMODE, (RFM69_readReg(REG_OPMODE) & 0xE3) | RF_OPMODE_SYNTHESIZER);
      break;
    case RF69_MODE_STANDBY:
      RFM69_writeReg(REG_OPMODE, (RFM69_readReg(REG_OPMODE) & 0xE3) | RF_OPMODE_STANDBY);
      break;
    case RF69_MODE_SLEEP:
      RFM69_writeReg(REG_OPMODE, (RFM69_readReg(REG_OPMODE) & 0xE3) | RF_OPMODE_SLEEP);
      break;
    default:
      return;
  }

  // we are using packet mode, so this check is not really needed
  // but waiting for mode ready is necessary when going from sleep because the FIFO may not be immediately available from previous mode
  while (_mode == RF69_MODE_SLEEP && (RFM69_readReg(REG_IRQFLAGS1) & RF_IRQFLAGS1_MODEREADY) == 0x00); // wait for ModeReady

  _mode = newMode;
}

//put transceiver in sleep mode to save battery - to wake or resume receiving just call RFM69_receiveDone()
void RFM69_sleep() {
  RFM69_setMode(RF69_MODE_SLEEP);
}

//set this node's address
void RFM69_setAddress(uint8_t addr)
{
  _address = addr;
  RFM69_writeReg(REG_NODEADRS, _address);
}

//set this node's network id
void RFM69_setNetwork(uint16_t networkID)
{
  RFM69_writeReg(REG_SYNCVALUE1, (uint8_t)(networkID & 0x00FF));
  RFM69_writeReg(REG_SYNCVALUE2, (uint8_t)(networkID >> 8));
}

// set *transmit/TX* output power: 0=min, 31=max
// this results in a "weaker" transmitted signal, and directly results in a lower RSSI at the receiver
// the power configurations are explained in the SX1231H datasheet (Table 10 on p21; RegPaLevel p66): http://www.semtech.com/images/datasheet/sx1231h.pdf
// valid powerLevel parameter values are 0-31 and result in a directly proportional effect on the output/transmission power
// this function implements 2 modes as follows:
//       - for RFM69W the range is from 0-31 [-18dBm to 13dBm] (PA0 only on RFIO pin)
//       - for RFM69HW the range is from 0-31 [5dBm to 20dBm]  (PA1 & PA2 on PA_BOOST pin & high Power PA settings - see section 3.3.7 in datasheet, p22)
void RFM69_setPowerLevel(uint8_t powerLevel)
{
  _powerLevel = (powerLevel > 31 ? 31 : powerLevel);
  if (ISRFM69HW)
  {
    _powerLevel /= 2;
  }
  RFM69_writeReg(REG_PALEVEL, (RFM69_readReg(REG_PALEVEL) & 0xE0) | _powerLevel);
}

bool RFM69_canSend()
{
  if (_mode == RF69_MODE_RX && payloadLen == 0 && RFM69_readRSSI(false) < CSMA_LIMIT) // if signal stronger than -100dBm is detected assume channel activity
  {
    RFM69_setMode(RF69_MODE_STANDBY);
    return true;
  }
  return false;
}

void RFM69_send(uint8_t toAddress, const void* buffer, uint8_t bufferSize, bool requestACK)
{
  RFM69_writeReg(REG_PACKETCONFIG2, (RFM69_readReg(REG_PACKETCONFIG2) & 0xFB) | RF_PACKET2_RXRESTART); // avoid RX deadlocks
  //uint32_t now = millis();
  while (!RFM69_canSend() /*&& millis() - now < RF69_CSMA_LIMIT_MS*/) RFM69_receiveDone();
  RFM69_sendFrame(toAddress, buffer, bufferSize, requestACK, false);
}

// to increase the chance of getting a packet across, call this function instead of send
// and it handles all the ACK requesting/retrying for you :)
// The only twist is that you have to manually listen to ACK requests on the other side and send back the ACKs
// The reason for the semi-automaton is that the lib is interrupt driven and
// requires user action to read the received data and decide what to do with it
// replies usually take only 5..8ms at 50kbps@915MHz
bool RFM69_sendWithRetry(uint8_t toAddress, const void* buffer, uint8_t bufferSize, uint8_t retries, uint8_t retryWaitTime)
{
  for (uint8_t i = 0; i <= retries; i++)
  {
    RFM69_send(toAddress, buffer, bufferSize, true);
    Timeout_SetTimeout1(retryWaitTime);
    while (!Timeout_IsTimeout1())
    {
      if (RFM69_ACKReceived(toAddress))
      {
        //Serial.print(" ~ms:"); Serial.print(millis() - sentTime);
        return true;
      }
    }
    //Serial.print(" RETRY#"); Serial.println(i + 1);
  }
  return false;
}

// should be polled immediately after sending a packet with ACK request
bool RFM69_ACKReceived(uint8_t fromNodeID)
{
  if (RFM69_receiveDone())
    return (senderID == fromNodeID || fromNodeID == RF69_BROADCAST_ADDR) && ACK_RECEIVED;
  return false;
}

// check whether an ACK was requested in the last received packet (non-broadcasted packet)
bool RFM69_ACKRequested()
{
  return ACK_Requested && (targetID != RF69_BROADCAST_ADDR);
}

// should be called immediately after reception in case sender wants ACK
void RFM69_sendACK(const void* buffer, uint8_t bufferSize)
{
  ACK_Requested = 0;   // TWS added to make sure we don't end up in a timing race and infinite loop sending Acks
  uint8_t sender = senderID;
  int16_t l_rssi = rssi; // save payload received RSSI value
  RFM69_writeReg(REG_PACKETCONFIG2, (RFM69_readReg(REG_PACKETCONFIG2) & 0xFB) | RF_PACKET2_RXRESTART); // avoid RX deadlocks
  Timeout_SetTimeout1(RF69_CSMA_LIMIT_MS);
  while (!RFM69_canSend() && !Timeout_IsTimeout1())
  {
    RFM69_receiveDone();
  }
  senderID = sender;    // TWS: Restore senderID after it gets wiped out by RFM69_receiveDone()
  RFM69_sendFrame(sender, buffer, bufferSize, false, true);
  rssi = l_rssi; // restore payload RSSI
}

// internal function
static void RFM69_sendFrame(uint8_t toAddress, const void* buffer, uint8_t bufferSize, bool requestACK, bool sendACK)
{
  RFM69_setMode(RF69_MODE_STANDBY); // turn off receiver to prevent reception while filling fifo
  while ((RFM69_readReg(REG_IRQFLAGS1) & RF_IRQFLAGS1_MODEREADY) == 0x00); // wait for ModeReady
  RFM69_writeReg(REG_DIOMAPPING1, RF_DIOMAPPING1_DIO0_00); // DIO0 is "Packet Sent"
  if (bufferSize > RF69_MAX_DATA_LEN) bufferSize = RF69_MAX_DATA_LEN;

  // control byte
  uint8_t CTLbyte = 0x00;
  if (sendACK)
    CTLbyte = RFM69_CTL_SENDACK;
  else if (requestACK)
    CTLbyte = RFM69_CTL_REQACK;

  // write to FIFO
  RFM69_select();
  SPI_transfer8(REG_FIFO | 0x80);
  SPI_transfer8(bufferSize + 3);
  SPI_transfer8(toAddress);
  SPI_transfer8(_address);
  SPI_transfer8(CTLbyte);

  for (uint8_t i = 0; i < bufferSize; i++)
    SPI_transfer8(((uint8_t*) buffer)[i]);
  RFM69_unselect();

  // no need to wait for transmit mode to be ready since its handled by the radio
  RFM69_setMode(RF69_MODE_TX);
  Timeout_SetTimeout1(RF69_TX_LIMIT_MS);
  while (RFM69_ReadDIO0Pin() == 0 && !Timeout_IsTimeout1()); // wait for DIO0 to turn HIGH signalling transmission finish
  //while (RFM69_readReg(REG_IRQFLAGS2) & RF_IRQFLAGS2_PACKETSENT == 0x00); // wait for ModeReady
  RFM69_setMode(RF69_MODE_STANDBY);
}

// internal function - interrupt gets called when a packet is received
void RFM69_interruptHandler() {

  if (_mode == RF69_MODE_RX && (RFM69_readReg(REG_IRQFLAGS2) & RF_IRQFLAGS2_PAYLOADREADY))
  {
    uint8_t CTLbyte;
    //rssi = RFM69_readRSSI();
    RFM69_setMode(RF69_MODE_STANDBY);
    RFM69_select();
    SPI_transfer8(REG_FIFO & 0x7F);
    payloadLen = SPI_transfer8(0);
    payloadLen = payloadLen > 66 ? 66 : payloadLen; // precaution
    targetID = SPI_transfer8(0);
    if(!(_promiscuousMode || targetID == _address || targetID == RF69_BROADCAST_ADDR) // match this node's address, or broadcast address or anything in promiscuous mode
       || payloadLen < 3) // address situation could receive packets that are malformed and don't fit this libraries extra fields
    {
      payloadLen = 0;
      RFM69_unselect();
      RFM69_receiveBegin();
      return;
    }

    datalen = payloadLen - 3;
    senderID = SPI_transfer8(0);
    CTLbyte = SPI_transfer8(0);

    ACK_RECEIVED = CTLbyte & RFM69_CTL_SENDACK; // extract ACK-received flag
    ACK_Requested = CTLbyte & RFM69_CTL_REQACK; // extract ACK-requested flag

    //interruptHook(CTLbyte);     // TWS: hook to derived class interrupt function

    for (uint8_t i = 0; i < datalen; i++)
    {
      data[i] = SPI_transfer8(0);
    }
    if (datalen < RF69_MAX_DATA_LEN) data[datalen] = 0; // add null at end of string
    RFM69_unselect();
    RFM69_setMode(RF69_MODE_RX);
  }
  rssi = RFM69_readRSSI(false);
}

// internal function
//void RFM69::isr0() { selfPointer->interruptHandler(); }

// internal function
void RFM69_receiveBegin()
{
  datalen = 0;
  senderID = 0;
  targetID = 0;
  payloadLen = 0;
  ACK_Requested = 0;
  ACK_RECEIVED = 0;
  rssi = 0;
  if (RFM69_readReg(REG_IRQFLAGS2) & RF_IRQFLAGS2_PAYLOADREADY)
    RFM69_writeReg(REG_PACKETCONFIG2, (RFM69_readReg(REG_PACKETCONFIG2) & 0xFB) | RF_PACKET2_RXRESTART); // avoid RX deadlocks
  RFM69_writeReg(REG_DIOMAPPING1, RF_DIOMAPPING1_DIO0_01); // set DIO0 to "PAYLOADREADY" in receive mode
  RFM69_setMode(RF69_MODE_RX);
}

// checks if a packet was received and/or puts transceiver in receive (ie RX or listen) mode
bool RFM69_receiveDone()
{
//ATOMIC_BLOCK(ATOMIC_FORCEON)
  //noInterrupts(); // re-enabled in RFM69_unselect() via setMode() or via RFM69_receiveBegin()
  RFM69_interruptHandler();
  if (_mode == RF69_MODE_RX && payloadLen > 0)
  {
    RFM69_setMode(RF69_MODE_STANDBY); // enables interrupts
    return true;
  }
  else if (_mode == RF69_MODE_RX) // already in RX no payload yet
  {
    //interrupts(); // explicitly re-enable interrupts
    return false;
  }
  RFM69_receiveBegin();
  return false;
}

// To enable encryption: radio.encrypt("ABCDEFGHIJKLMNOP");
// To disable encryption: radio.encrypt(null) or radio.encrypt(0)
// KEY HAS TO BE 16 bytes !!!
void RFM69_encrypt(const char* key)
{
  RFM69_setMode(RF69_MODE_STANDBY);
  if (key != 0)
  {
    RFM69_select();
    SPI_transfer8(REG_AESKEY1 | 0x80);
    for (uint8_t i = 0; i < 16; i++)
      SPI_transfer8(key[i]);
    RFM69_unselect();
  }
  RFM69_writeReg(REG_PACKETCONFIG2, (RFM69_readReg(REG_PACKETCONFIG2) & 0xFE) | (key ? 1 : 0));
}

// get the received signal strength indicator (RSSI)
int16_t RFM69_readRSSI(bool forceTrigger) {
  int16_t rssi = 0;
  if (forceTrigger)
  {
    // RSSI trigger not needed if DAGC is in continuous mode
    RFM69_writeReg(REG_RSSICONFIG, RF_RSSI_START);
    while ((RFM69_readReg(REG_RSSICONFIG) & RF_RSSI_DONE) == 0x00); // wait for RSSI_Ready
  }
  rssi = -RFM69_readReg(REG_RSSIVALUE);
  rssi >>= 1;
  return rssi;
}

// true  = disable filtering to capture all frames on network
// false = enable node/broadcast filtering to capture only frames sent to this/broadcast address
void RFM69_promiscuous(bool onOff)
{
  _promiscuousMode = onOff;
  //RFM69_writeReg(REG_PACKETCONFIG1, (RFM69_readReg(REG_PACKETCONFIG1) & 0xF9) | (onOff ? RF_PACKET1_ADRSFILTERING_OFF : RF_PACKET1_ADRSFILTERING_NODEBROADCAST));
}
/*
// for RFM69HW only: you must call RFM69_setHighPower(true) after initialize() or else transmission won't work
void RFM69_setHighPower(bool onOff) {
  RFM69_writeReg(REG_OCP, ISRFM69HW ? RF_OCP_OFF : RF_OCP_ON);
  if (ISRFM69HW) // turning ON
    RFM69_writeReg(REG_PALEVEL, (RFM69_readReg(REG_PALEVEL) & 0x1F) | RF_PALEVEL_PA1_ON | RF_PALEVEL_PA2_ON); // enable P1 & P2 amplifier stages
  else
    RFM69_writeReg(REG_PALEVEL, RF_PALEVEL_PA0_ON | RF_PALEVEL_PA1_OFF | RF_PALEVEL_PA2_OFF | _powerLevel); // enable P0 only
}

// internal function
void RFM69_setHighPowerRegs(bool onOff)
{
  RFM69_writeReg(REG_TESTPA1, onOff ? 0x5D : 0x55);
  RFM69_writeReg(REG_TESTPA2, onOff ? 0x7C : 0x70);
}
*/
// for RFM69HW only: you must call RFM69_setHighPower() after initialize() or else transmission won't work
void RFM69_setHighPower()
{
  RFM69_writeReg(REG_OCP, ISRFM69HW ? RF_OCP_OFF : RF_OCP_ON);
  #if (ISRFM69HW == 1) // turning ON
    RFM69_writeReg(REG_PALEVEL, (RFM69_readReg(REG_PALEVEL) & 0x1F) | RF_PALEVEL_PA1_ON | RF_PALEVEL_PA2_ON); // enable P1 & P2 amplifier stages

  #elseif {
    RFM69_writeReg(REG_PALEVEL, RF_PALEVEL_PA0_ON | RF_PALEVEL_PA1_OFF | RF_PALEVEL_PA2_OFF | _powerLevel); // enable P0 only
}
  #endif
}

// internal function
void RFM69_setHighPowerRegs(bool onOff)
{
  RFM69_writeReg(REG_TESTPA1, onOff ? 0x5D : 0x55);
  RFM69_writeReg(REG_TESTPA2, onOff ? 0x7C : 0x70);
}

// for debugging
#define REGISTER_DETAIL 1

void RFM69_readAllRegs() {
  uint8_t regVal;

#if REGISTER_DETAIL
  uint16_t capVal;

  //... State Variables for intelligent decoding
  uint8_t modeFSK = 0;
  uint64_t bitRate = 0;
  uint32_t freqDev = 0;
  uint32_t freqCenter = 0;
#endif
  char pcBuf[130];
  debug_printf("\r\n");

  uint8_t regAddr;
  debug_printf("Address | HEX\r\n");
  for (regAddr = 1; regAddr <= 0x4F; regAddr++) {
    RFM69_select();
    SPI_transfer8(regAddr & 0x7F); // send address + r/w bit
    regVal = SPI_transfer8(0);
    RFM69_unselect();

    sprintf(log_buffer,"%02X|%02X : ", regAddr, regVal);
    debug_printf(log_buffer);

#if REGISTER_DETAIL
    switch (regAddr) {
    case 0x1: {
      debug_printf("Controls the automatic Sequencer ( see section 4.2 "
                  ")\r\nSequencerOff : ");
      if (0x80 & regVal) {
        debug_printf("1 -> Mode is forced by the user\r\n");
      } else {
        debug_printf(
            "0 -> Operating mode as selected with Mode bits in RegOpMode is "
            "automatically reached with the Sequencer\r\n");
      }

      debug_printf("\r\nEnables Listen mode, should be enabled whilst in "
                  "Standby mode:\r\nListenOn : ");
      if (0x40 & regVal) {
        debug_printf("1 -> On\r\n");
      } else {
        debug_printf("0 -> Off ( see section 4.3)\r\n");
      }

      debug_printf("\r\nAborts Listen mode when set together with ListenOn=0 "
                  "See section 4.3.4 for details (Always reads 0.)\r\n");
      if (0x20 & regVal) {
        debug_printf("ERROR - ListenAbort should NEVER return 1 this is a write "
                    "only register\r\n");
      }

      debug_printf("\r\nTransceiver's operating modes:\r\nMode : ");
      capVal = (regVal >> 2) & 0x7;
      if (capVal == 0x0) {
        debug_printf("000 -> Sleep mode (SLEEP)\r\n");
      } else if (capVal == 0b001) {
        debug_printf("001 -> Standby mode (STDBY)\r\n");
      } else if (capVal == 0b010) {
        debug_printf("010 -> Frequency Synthesizer mode (FS)\r\n");
      } else if (capVal == 0b011) {
        debug_printf("011 -> Transmitter mode (TX)\r\n");
      } else if (capVal == 0b100) {
        debug_printf("100 -> Receiver Mode (RX)\r\n");
      } else {
        // debug_printf( capVal, BIN );
        sprintf(log_buffer,"%02X -> RESERVED\n", capVal );
        debug_printf(log_buffer);
      }
      debug_printf("\r\n");
      break;
    }

    case 0x2: {

      debug_printf("Data Processing mode:\r\nDataMode : ");
      capVal = (regVal >> 5) & 0x3;
      if (capVal == 0b00) {
        debug_printf("00 -> Packet mode\r\n");
      } else if (capVal == 0b01) {
        debug_printf("01 -> reserved\r\n");
      } else if (capVal == 0b10) {
        debug_printf("10 -> Continuous mode with bit synchronizer\r\n");
      } else if (capVal == 0b11) {
        debug_printf("11 -> Continuous mode without bit synchronizer\r\n");
      }

      debug_printf("\r\nModulation scheme:\r\nModulation Type : ");
      capVal = (regVal >> 3) & 0x3;
      if (capVal == 0b00) {
        debug_printf("00 -> FSK\r\n");
        modeFSK = 1;
      } else if (capVal == 0b01) {
        debug_printf("01 -> OOK\r\n");
      } else if (capVal == 0b10) {
        debug_printf("10 -> reserved\r\n");
      } else if (capVal == 0b11) {
        debug_printf("11 -> reserved\r\n");
      }

      debug_printf("\r\nData shaping: ");
      if (modeFSK) {
        debug_printf("in FSK:\r\n");
      } else {
        debug_printf("in OOK:\r\n");
      }
      debug_printf("ModulationShaping : ");
      capVal = regVal & 0x3;
      if (modeFSK) {
        if (capVal == 0b00) {
          debug_printf("00 -> no shaping\r\n");
        } else if (capVal == 0b01) {
          debug_printf("01 -> Gaussian filter, BT = 1.0\r\n");
        } else if (capVal == 0b10) {
          debug_printf("10 -> Gaussian filter, BT = 0.5\r\n");
        } else if (capVal == 0b11) {
          debug_printf("11 -> Gaussian filter, BT = 0.3\r\n");
        }
      } else {
        if (capVal == 0b00) {
          debug_printf("00 -> no shaping\r\n");
        } else if (capVal == 0b01) {
          debug_printf("01 -> filtering with f(cutoff) = BR\r\n");
        } else if (capVal == 0b10) {
          debug_printf("10 -> filtering with f(cutoff) = 2*BR\r\n");
        } else if (capVal == 0b11) {
          debug_printf("ERROR - 11 is reserved\r\n");
        }
      }

      debug_printf("\r\n");
      break;
    }

    case 0x3: {
      bitRate = (regVal << 8);
      break;
    }

    case 0x4: {
      bitRate |= regVal;
      debug_printf("Bit Rate (Chip Rate when Manchester encoding is enabled)\r\nBitRate : ");
      uint64_t val = 32UL * 1000UL * 1000UL / bitRate;
      sprintf(pcBuf, "%lld", val);
      debug_printf(pcBuf);
      debug_printf("\r\n");
      break;
    }

    case 0x5: {
      freqDev = ((regVal & 0x3f) << 8);
      break;
    }

    case 0x6: {
      freqDev |= regVal;
      debug_printf("Frequency deviation\r\nFdev : ");
      uint32_t val = 61UL * freqDev;
      sprintf(pcBuf, "%ld", val);
      debug_printf(pcBuf);
      debug_printf("\r\n");
      break;
    }

    case 0x7: {
      unsigned long tempVal = regVal;
      freqCenter = (tempVal << 16);
      break;
    }

    case 0x8: {
      unsigned long tempVal = regVal;
      freqCenter = freqCenter | (tempVal << 8);
      break;
    }

    case 0x9: {
      freqCenter = freqCenter | regVal;
      debug_printf("RF Carrier frequency\r\nFRF : ");
      uint32_t val = 61UL * freqCenter;
      sprintf(pcBuf, "%ld", val);
      debug_printf(pcBuf);
      debug_printf("\r\n");
      break;
    }

    case 0xa: {
      debug_printf("RC calibration control & status\r\nRcCalDone : ");
      if (0x40 & regVal) {
        debug_printf("1 -> RC calibration is over\r\n");
      } else {
        debug_printf("0 -> RC calibration is in progress\r\n");
      }

      debug_printf("\r\n");
      break;
    }

    case 0xb: {
      debug_printf(
          "Improved AFC routine for signals with modulation index lower than "
          "2.  Refer to section 3.4.16 for details\r\nAfcLowBetaOn : ");
      if (0x20 & regVal) {
        debug_printf("1 -> Improved AFC routine\r\n");
      } else {
        debug_printf("0 -> Standard AFC routine\r\n");
      }
      debug_printf("\r\n");
      break;
    }

    case 0xc: {
      debug_printf("Reserved\r\n");
      break;
    }

    case 0xd: {
      uint8_t val;
      debug_printf("Resolution of Listen mode Idle time (calibrated RC osc):\r\nListenResolIdle : ");
      val = regVal >> 6;
      if (val == 0b00) {
        debug_printf("00 -> reserved\r\n");
      } else if (val == 0b01) {
        debug_printf("01 -> 64 us\r\n");
      } else if (val == 0b10) {
        debug_printf("10 -> 4.1 ms\r\n");
      } else if (val == 0b11) {
        debug_printf("11 -> 262 ms\r\n");
      }

      debug_printf("\r\nResolution of Listen mode Rx time (calibrated RC osc):\r\nListenResolRx : ");
      val = (regVal >> 4) & 0x3;
      if (val == 0b00) {
        debug_printf("00 -> reserved\r\n");
      } else if (val == 0b01) {
        debug_printf("01 -> 64 us\r\n");
      } else if (val == 0b10) {
        debug_printf("10 -> 4.1 ms\r\n");
      } else if (val == 0b11) {
        debug_printf("11 -> 262 ms\r\n");
      }

      debug_printf("\r\nCriteria for packet acceptance in Listen mode:\r\nListenCriteria : ");
      if (0x8 & regVal) {
        debug_printf("1 -> signal strength is above RssiThreshold and "
                    "SyncAddress matched\r\n");
      } else {
        debug_printf("0 -> signal strength is above RssiThreshold\r\n");
      }

      debug_printf("\r\nAction taken after acceptance of a packet in Listen mode:\r\nListenEnd : ");
      val = (regVal >> 1) & 0x3;
      if (val == 0b00) {
        debug_printf("00 -> chip stays in Rx mode. Listen mode stops and must be disabled (see section 4.3)\r\n");
      } else if (val == 0b01) {
        debug_printf(
            "01 -> chip stays in Rx mode until PayloadReady or Timeout \r\n"
            "interrupt occurs.  It then goes to the mode defined by Mode. \r\n"
            "Listen mode stops and must be disabled (see section 4.3)\r\n");
      } else if (val == 0b10) {
        debug_printf("10 -> chip stays in Rx mode until PayloadReady or Timeout "
                    "occurs.  Listen mode then resumes in Idle state.  FIFO "
                    "content is lost at next Rx wakeup.\r\n");
      } else if (val == 0b11) {
        debug_printf("11 -> Reserved\r\n");
      }
      debug_printf("\r\n");


      break;
    }

    default: {}
    }

#endif
  }
  RFM69_unselect();
  debug_printf("\r\n");
  debug_printf("end read all regs\r\n");
}

uint8_t RFM69_readTemperature(uint8_t calFactor) // returns centigrade
{
  RFM69_setMode(RF69_MODE_STANDBY);
  RFM69_writeReg(REG_TEMP1, RF_TEMP1_MEAS_START);
  while ((RFM69_readReg(REG_TEMP1) & RF_TEMP1_MEAS_RUNNING));
  return ~RFM69_readReg(REG_TEMP2) + COURSE_TEMP_COEF + calFactor; // 'complement' corrects the slope, rising temp = rising val
} // COURSE_TEMP_COEF puts reading in the ballpark, user can add additional correction

void RFM69_rcCalibration()
{
  RFM69_writeReg(REG_OSC1, RF_OSC1_RCCAL_START);
  while ((RFM69_readReg(REG_OSC1) & RF_OSC1_RCCAL_DONE) == 0x00);
}

uint8_t RFM69_readReg(uint8_t addr)
{
  uint8_t regval;
  RFM69_select();
  SPI_transfer8(addr & 0x7F);
  regval = SPI_transfer8(0);
  RFM69_unselect();
  return regval;
}

void RFM69_writeReg(uint8_t addr, uint8_t value)
{
  RFM69_select();
  SPI_transfer8(addr | 0x80);
  SPI_transfer8(value);
  RFM69_unselect();
}

// select the RFM69 transceiver (save SPI settings, set CS low)
void RFM69_select()
{
  noInterrupts();
  RFM69_SetCSPin(0);
}

// unselect the RFM69 transceiver (set CS high, restore SPI settings)
void RFM69_unselect()
{
  RFM69_SetCSPin(1);
  interrupts();
}


// for the STM32, simple decoding of radio payloads into structs must happen in 4-byte blocks to avoid padding issues.
// Valid types are: Long, Unsigned Long, and Float.
// https://stackoverflow.com/questions/119123/why-isnt-sizeof-for-a-struct-equal-to-the-sum-of-sizeof-of-each-member
typedef struct {
  uint32_t nodeId; // store this nodeId
  uint32_t uptime; // uptime in ms
} dataSTR;
dataSTR theData;
// function below
void PrintStruct(void) {
  if (datalen != sizeof(dataSTR)) {
    debug_printf("Invalid payload received, not matching data struct!\r\n");
    }
  else {
    theData = *(dataSTR *)data;
    sprintf(log_buffer, " nodeId=%ld\r\n", theData.nodeId);
    debug_printf(log_buffer);
    sprintf(log_buffer, " uptime=%ld\r\n", theData.uptime);
    debug_printf(log_buffer);
    //sprintf(log_buffer, " size of the struct=%d\r\n", sizeof(PayloadSTR));
    //debug_printf(log_buffer); // 12
  }
}


// if the sending device is setup to send data structures NOT multiples of 4-bytes,
// this is a manual method for decoding each byte into the relevant datatypes
uint16_t firstdata = 0;
uint32_t seconddata = 0;
void PrintByteByByte(void) {
  firstdata = RFM69_DATA(0) + (RFM69_DATA(1) << 8);
  seconddata = RFM69_DATA(2) + (RFM69_DATA(3) << 8) + (RFM69_DATA(4) << 16) + (RFM69_DATA(5) << 24);
  sprintf(log_buffer, "first_data: %d\r\n", firstdata);
  debug_printf(log_buffer);
  sprintf(log_buffer, "second_data: %ld\r\n", seconddata);
  debug_printf(log_buffer);
}


// printing the raw bytes as received.
void PrintRawBytes(void) {
  for (int i = 0; i < datalen; i++) {
    sprintf(log_buffer, "Byte%d Value: %d\r\n", i, RFM69_DATA(i));
    debug_printf(log_buffer);
  }
  // debugging
  //sprintf(log_buffer, "PayloadLen = %d\r\n", payloadLen);
  //debug_printf(log_buffer);
  //sprintf(log_buffer, "datalen %d\r\n", datalen);
  //debug_printf(log_buffer);
}
