openenergymonitor/STM32/Software/Sombrero_VE_STM32full_rf69n/Src/adc.c

/**
  ******************************************************************************
  * File Name          : ADC.c
  * Description        : This file provides code for the configuration
  *                      of the ADC instances.
  ******************************************************************************
  ** This notice applies to any and all portions of this file
  * that are not between comment pairs USER CODE BEGIN and
  * USER CODE END. Other portions of this file, whether 
  * inserted by the user or by software development tools
  * are owned by their respective copyright owners.
  *
  * COPYRIGHT(c) 2020 STMicroelectronics
  *
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
  ******************************************************************************
  */

/* Includes ------------------------------------------------------------------*/
#include "adc.h"

#include "gpio.h"
#include "dma.h"

/* USER CODE BEGIN 0 */
#include <stdbool.h>
#include <stdlib.h>
#include "tim.h"
#include "usart.h"
int32_t usec_lag = 95;  // how many microseconds to pull the voltage channel back by.
                    // this is a single value for phase correction for both voltage and current ADCs, effecting all CT and VT channels.
//int32_t usec_lag = 0;

uint16_t const adc_buff_size = CTn * ADC_DMA_BUFFSIZE_PERCHANNEL;
uint16_t const adc_buff_half_size = (CTn * ADC_DMA_BUFFSIZE_PERCHANNEL) / 2;
uint16_t adc1_dma_buff[CTn * ADC_DMA_BUFFSIZE_PERCHANNEL];
uint16_t adc3_dma_buff[CTn * ADC_DMA_BUFFSIZE_PERCHANNEL];
//uint16_t adc4_dma_buff[ADC_DMA_BUFFSIZE_PERCHANNEL];

bool adc_buffer_overflow = 0;
/* USER CODE END 0 */

ADC_HandleTypeDef hadc1;
ADC_HandleTypeDef hadc2;
ADC_HandleTypeDef hadc3;
ADC_HandleTypeDef hadc4;
DMA_HandleTypeDef hdma_adc1;
DMA_HandleTypeDef hdma_adc2;
DMA_HandleTypeDef hdma_adc3;

/* ADC1 init function */
void MX_ADC1_Init(void)
{
  ADC_MultiModeTypeDef multimode;
  ADC_ChannelConfTypeDef sConfig;

    /**Common config 
    */
  hadc1.Instance = ADC1;
  hadc1.Init.ClockPrescaler = ADC_CLOCK_SYNC_PCLK_DIV4;
  hadc1.Init.Resolution = ADC_RESOLUTION_12B;
  hadc1.Init.ScanConvMode = ADC_SCAN_DISABLE;
  hadc1.Init.ContinuousConvMode = ENABLE;
  hadc1.Init.DiscontinuousConvMode = DISABLE;
  hadc1.Init.ExternalTrigConvEdge = ADC_EXTERNALTRIGCONVEDGE_FALLING;
  hadc1.Init.ExternalTrigConv = ADC_EXTERNALTRIGCONV_T8_TRGO2;
  hadc1.Init.DataAlign = ADC_DATAALIGN_RIGHT;
  hadc1.Init.NbrOfConversion = 1;
  hadc1.Init.DMAContinuousRequests = ENABLE;
  hadc1.Init.EOCSelection = ADC_EOC_SEQ_CONV;
  hadc1.Init.LowPowerAutoWait = DISABLE;
  hadc1.Init.Overrun = ADC_OVR_DATA_OVERWRITTEN;
  if (HAL_ADC_Init(&hadc1) != HAL_OK)
  {
    _Error_Handler(__FILE__, __LINE__);
  }

    /**Configure the ADC multi-mode 
    */
  multimode.Mode = ADC_MODE_INDEPENDENT;
  if (HAL_ADCEx_MultiModeConfigChannel(&hadc1, &multimode) != HAL_OK)
  {
    _Error_Handler(__FILE__, __LINE__);
  }

    /**Configure Regular Channel 
    */
  sConfig.Channel = ADC_CHANNEL_1;
  sConfig.Rank = ADC_REGULAR_RANK_1;
  sConfig.SingleDiff = ADC_SINGLE_ENDED;
  sConfig.SamplingTime = ADC_SAMPLETIME_181CYCLES_5;
  sConfig.OffsetNumber = ADC_OFFSET_NONE;
  sConfig.Offset = 0;
  if (HAL_ADC_ConfigChannel(&hadc1, &sConfig) != HAL_OK)
  {
    _Error_Handler(__FILE__, __LINE__);
  }

}
/* ADC2 init function */
void MX_ADC2_Init(void)
{
  ADC_ChannelConfTypeDef sConfig;

    /**Common config 
    */
  hadc2.Instance = ADC2;
  hadc2.Init.ClockPrescaler = ADC_CLOCK_SYNC_PCLK_DIV4;
  hadc2.Init.Resolution = ADC_RESOLUTION_12B;
  hadc2.Init.ScanConvMode = ADC_SCAN_ENABLE;
  hadc2.Init.ContinuousConvMode = ENABLE;
  hadc2.Init.DiscontinuousConvMode = DISABLE;
  hadc2.Init.ExternalTrigConvEdge = ADC_EXTERNALTRIGCONVEDGE_FALLING;
  hadc2.Init.ExternalTrigConv = ADC_EXTERNALTRIGCONV_T8_TRGO2;
  hadc2.Init.DataAlign = ADC_DATAALIGN_RIGHT;
  hadc2.Init.NbrOfConversion = 3;
  hadc2.Init.DMAContinuousRequests = ENABLE;
  hadc2.Init.EOCSelection = ADC_EOC_SEQ_CONV;
  hadc2.Init.LowPowerAutoWait = DISABLE;
  hadc2.Init.Overrun = ADC_OVR_DATA_OVERWRITTEN;
  if (HAL_ADC_Init(&hadc2) != HAL_OK)
  {
    _Error_Handler(__FILE__, __LINE__);
  }

    /**Configure Regular Channel 
    */
  sConfig.Channel = ADC_CHANNEL_2;
  sConfig.Rank = ADC_REGULAR_RANK_1;
  sConfig.SingleDiff = ADC_SINGLE_ENDED;
  sConfig.SamplingTime = ADC_SAMPLETIME_181CYCLES_5;
  sConfig.OffsetNumber = ADC_OFFSET_NONE;
  sConfig.Offset = 0;
  if (HAL_ADC_ConfigChannel(&hadc2, &sConfig) != HAL_OK)
  {
    _Error_Handler(__FILE__, __LINE__);
  }

    /**Configure Regular Channel 
    */
  sConfig.Channel = ADC_CHANNEL_3;
  sConfig.Rank = ADC_REGULAR_RANK_2;
  if (HAL_ADC_ConfigChannel(&hadc2, &sConfig) != HAL_OK)
  {
    _Error_Handler(__FILE__, __LINE__);
  }

    /**Configure Regular Channel 
    */
  sConfig.Channel = ADC_CHANNEL_4;
  sConfig.Rank = ADC_REGULAR_RANK_3;
  if (HAL_ADC_ConfigChannel(&hadc2, &sConfig) != HAL_OK)
  {
    _Error_Handler(__FILE__, __LINE__);
  }

}
/* ADC3 init function */
void MX_ADC3_Init(void)
{
  ADC_MultiModeTypeDef multimode;
  ADC_ChannelConfTypeDef sConfig;

    /**Common config 
    */
  hadc3.Instance = ADC3;
  hadc3.Init.ClockPrescaler = ADC_CLOCK_SYNC_PCLK_DIV4;
  hadc3.Init.Resolution = ADC_RESOLUTION_12B;
  hadc3.Init.ScanConvMode = ADC_SCAN_ENABLE;
  hadc3.Init.ContinuousConvMode = ENABLE;
  hadc3.Init.DiscontinuousConvMode = DISABLE;
  hadc3.Init.ExternalTrigConvEdge = ADC_EXTERNALTRIGCONVEDGE_RISING;
  hadc3.Init.ExternalTrigConv = ADC_EXTERNALTRIGCONV_T8_TRGO2;
  hadc3.Init.DataAlign = ADC_DATAALIGN_RIGHT;
  hadc3.Init.NbrOfConversion = 9;
  hadc3.Init.DMAContinuousRequests = ENABLE;
  hadc3.Init.EOCSelection = ADC_EOC_SEQ_CONV;
  hadc3.Init.LowPowerAutoWait = DISABLE;
  hadc3.Init.Overrun = ADC_OVR_DATA_OVERWRITTEN;
  if (HAL_ADC_Init(&hadc3) != HAL_OK)
  {
    _Error_Handler(__FILE__, __LINE__);
  }

    /**Configure the ADC multi-mode 
    */
  multimode.Mode = ADC_MODE_INDEPENDENT;
  if (HAL_ADCEx_MultiModeConfigChannel(&hadc3, &multimode) != HAL_OK)
  {
    _Error_Handler(__FILE__, __LINE__);
  }

    /**Configure Regular Channel 
    */
  sConfig.Channel = ADC_CHANNEL_12;
  sConfig.Rank = ADC_REGULAR_RANK_1;
  sConfig.SingleDiff = ADC_SINGLE_ENDED;
  sConfig.SamplingTime = ADC_SAMPLETIME_181CYCLES_5;
  sConfig.OffsetNumber = ADC_OFFSET_NONE;
  sConfig.Offset = 0;
  if (HAL_ADC_ConfigChannel(&hadc3, &sConfig) != HAL_OK)
  {
    _Error_Handler(__FILE__, __LINE__);
  }

    /**Configure Regular Channel 
    */
  sConfig.Channel = ADC_CHANNEL_1;
  sConfig.Rank = ADC_REGULAR_RANK_2;
  if (HAL_ADC_ConfigChannel(&hadc3, &sConfig) != HAL_OK)
  {
    _Error_Handler(__FILE__, __LINE__);
  }

    /**Configure Regular Channel 
    */
  sConfig.Channel = ADC_CHANNEL_13;
  sConfig.Rank = ADC_REGULAR_RANK_3;
  if (HAL_ADC_ConfigChannel(&hadc3, &sConfig) != HAL_OK)
  {
    _Error_Handler(__FILE__, __LINE__);
  }

    /**Configure Regular Channel 
    */
  sConfig.Channel = ADC_CHANNEL_6;
  sConfig.Rank = ADC_REGULAR_RANK_4;
  if (HAL_ADC_ConfigChannel(&hadc3, &sConfig) != HAL_OK)
  {
    _Error_Handler(__FILE__, __LINE__);
  }

    /**Configure Regular Channel 
    */
  sConfig.Channel = ADC_CHANNEL_2;
  sConfig.Rank = ADC_REGULAR_RANK_5;
  if (HAL_ADC_ConfigChannel(&hadc3, &sConfig) != HAL_OK)
  {
    _Error_Handler(__FILE__, __LINE__);
  }

    /**Configure Regular Channel 
    */
  sConfig.Channel = ADC_CHANNEL_14;
  sConfig.Rank = ADC_REGULAR_RANK_6;
  if (HAL_ADC_ConfigChannel(&hadc3, &sConfig) != HAL_OK)
  {
    _Error_Handler(__FILE__, __LINE__);
  }

    /**Configure Regular Channel 
    */
  sConfig.Channel = ADC_CHANNEL_15;
  sConfig.Rank = ADC_REGULAR_RANK_7;
  if (HAL_ADC_ConfigChannel(&hadc3, &sConfig) != HAL_OK)
  {
    _Error_Handler(__FILE__, __LINE__);
  }

    /**Configure Regular Channel 
    */
  sConfig.Channel = ADC_CHANNEL_16;
  sConfig.Rank = ADC_REGULAR_RANK_8;
  if (HAL_ADC_ConfigChannel(&hadc3, &sConfig) != HAL_OK)
  {
    _Error_Handler(__FILE__, __LINE__);
  }

    /**Configure Regular Channel 
    */
  sConfig.Channel = ADC_CHANNEL_3;
  sConfig.Rank = ADC_REGULAR_RANK_9;
  if (HAL_ADC_ConfigChannel(&hadc3, &sConfig) != HAL_OK)
  {
    _Error_Handler(__FILE__, __LINE__);
  }

}
/* ADC4 init function */
void MX_ADC4_Init(void)
{
  ADC_ChannelConfTypeDef sConfig;

    /**Common config 
    */
  hadc4.Instance = ADC4;
  hadc4.Init.ClockPrescaler = ADC_CLOCK_SYNC_PCLK_DIV4;
  hadc4.Init.Resolution = ADC_RESOLUTION_12B;
  hadc4.Init.ScanConvMode = ADC_SCAN_DISABLE;
  hadc4.Init.ContinuousConvMode = DISABLE;
  hadc4.Init.DiscontinuousConvMode = DISABLE;
  hadc4.Init.ExternalTrigConvEdge = ADC_EXTERNALTRIGCONVEDGE_NONE;
  hadc4.Init.ExternalTrigConv = ADC_SOFTWARE_START;
  hadc4.Init.DataAlign = ADC_DATAALIGN_RIGHT;
  hadc4.Init.NbrOfConversion = 1;
  hadc4.Init.DMAContinuousRequests = DISABLE;
  hadc4.Init.EOCSelection = ADC_EOC_SINGLE_CONV;
  hadc4.Init.LowPowerAutoWait = DISABLE;
  hadc4.Init.Overrun = ADC_OVR_DATA_OVERWRITTEN;
  if (HAL_ADC_Init(&hadc4) != HAL_OK)
  {
    _Error_Handler(__FILE__, __LINE__);
  }

    /**Configure Regular Channel 
    */
  sConfig.Channel = ADC_CHANNEL_11;
  sConfig.Rank = ADC_REGULAR_RANK_1;
  sConfig.SingleDiff = ADC_SINGLE_ENDED;
  sConfig.SamplingTime = ADC_SAMPLETIME_4CYCLES_5;
  sConfig.OffsetNumber = ADC_OFFSET_NONE;
  sConfig.Offset = 0;
  if (HAL_ADC_ConfigChannel(&hadc4, &sConfig) != HAL_OK)
  {
    _Error_Handler(__FILE__, __LINE__);
  }

}

static uint32_t HAL_RCC_ADC12_CLK_ENABLED=0;
static uint32_t HAL_RCC_ADC34_CLK_ENABLED=0;

void HAL_ADC_MspInit(ADC_HandleTypeDef* adcHandle)
{

  GPIO_InitTypeDef GPIO_InitStruct;
  if(adcHandle->Instance==ADC1)
  {
    /* ADC1 clock enable */
    HAL_RCC_ADC12_CLK_ENABLED++;
    if(HAL_RCC_ADC12_CLK_ENABLED==1){
      __HAL_RCC_ADC12_CLK_ENABLE();
    }
  
    /**ADC1 GPIO Configuration    
    PA0     ------> ADC1_IN1 
    */
    GPIO_InitStruct.Pin = SINGLEPHASE_Pin;
    GPIO_InitStruct.Mode = GPIO_MODE_ANALOG;
    GPIO_InitStruct.Pull = GPIO_NOPULL;
    HAL_GPIO_Init(SINGLEPHASE_GPIO_Port, &GPIO_InitStruct);

    /* ADC1 DMA Init */
    /* ADC1 Init */
    hdma_adc1.Instance = DMA1_Channel1;
    hdma_adc1.Init.Direction = DMA_PERIPH_TO_MEMORY;
    hdma_adc1.Init.PeriphInc = DMA_PINC_DISABLE;
    hdma_adc1.Init.MemInc = DMA_MINC_ENABLE;
    hdma_adc1.Init.PeriphDataAlignment = DMA_PDATAALIGN_HALFWORD;
    hdma_adc1.Init.MemDataAlignment = DMA_MDATAALIGN_HALFWORD;
    hdma_adc1.Init.Mode = DMA_CIRCULAR;
    hdma_adc1.Init.Priority = DMA_PRIORITY_HIGH;
    if (HAL_DMA_Init(&hdma_adc1) != HAL_OK)
    {
      _Error_Handler(__FILE__, __LINE__);
    }

    __HAL_LINKDMA(adcHandle,DMA_Handle,hdma_adc1);

    /* ADC1 interrupt Init */
    HAL_NVIC_SetPriority(ADC1_2_IRQn, 0, 0);
    HAL_NVIC_EnableIRQ(ADC1_2_IRQn);
  }
  else if(adcHandle->Instance==ADC2)
  {
    /* ADC2 clock enable */
    HAL_RCC_ADC12_CLK_ENABLED++;
    if(HAL_RCC_ADC12_CLK_ENABLED==1){
      __HAL_RCC_ADC12_CLK_ENABLE();
    }
  
    /**ADC2 GPIO Configuration    
    PA5     ------> ADC2_IN2
    PA6     ------> ADC2_IN3
    PA7     ------> ADC2_IN4 
    */
    GPIO_InitStruct.Pin = THREEPHASE1_Pin|THREEPHASE2_Pin|THREEPHASE3_Pin;
    GPIO_InitStruct.Mode = GPIO_MODE_ANALOG;
    GPIO_InitStruct.Pull = GPIO_NOPULL;
    HAL_GPIO_Init(GPIOA, &GPIO_InitStruct);

    /* ADC2 DMA Init */
    /* ADC2 Init */
    hdma_adc2.Instance = DMA2_Channel1;
    hdma_adc2.Init.Direction = DMA_PERIPH_TO_MEMORY;
    hdma_adc2.Init.PeriphInc = DMA_PINC_DISABLE;
    hdma_adc2.Init.MemInc = DMA_MINC_ENABLE;
    hdma_adc2.Init.PeriphDataAlignment = DMA_PDATAALIGN_HALFWORD;
    hdma_adc2.Init.MemDataAlignment = DMA_MDATAALIGN_HALFWORD;
    hdma_adc2.Init.Mode = DMA_CIRCULAR;
    hdma_adc2.Init.Priority = DMA_PRIORITY_HIGH;
    if (HAL_DMA_Init(&hdma_adc2) != HAL_OK)
    {
      _Error_Handler(__FILE__, __LINE__);
    }

    __HAL_LINKDMA(adcHandle,DMA_Handle,hdma_adc2);

    /* ADC2 interrupt Init */
    HAL_NVIC_SetPriority(ADC1_2_IRQn, 0, 0);
    HAL_NVIC_EnableIRQ(ADC1_2_IRQn);
  }
  else if(adcHandle->Instance==ADC3)
  {
    /* ADC3 clock enable */
    HAL_RCC_ADC34_CLK_ENABLED++;
    if(HAL_RCC_ADC34_CLK_ENABLED==1){
      __HAL_RCC_ADC34_CLK_ENABLE();
    }
  
    /**ADC3 GPIO Configuration    
    PB0     ------> ADC3_IN12
    PB1     ------> ADC3_IN1
    PE7     ------> ADC3_IN13
    PE8     ------> ADC3_IN6
    PE9     ------> ADC3_IN2
    PE10     ------> ADC3_IN14
    PE11     ------> ADC3_IN15
    PE12     ------> ADC3_IN16
    PE13     ------> ADC3_IN3
    PD14     ------> ADC3_IN11 
    */
    GPIO_InitStruct.Pin = GPIO_PIN_0|GPIO_PIN_1;
    GPIO_InitStruct.Mode = GPIO_MODE_ANALOG;
    GPIO_InitStruct.Pull = GPIO_NOPULL;
    HAL_GPIO_Init(GPIOB, &GPIO_InitStruct);

    GPIO_InitStruct.Pin = GPIO_PIN_7|GPIO_PIN_8|GPIO_PIN_9|GPIO_PIN_10 
                          |GPIO_PIN_11|GPIO_PIN_12|GPIO_PIN_13;
    GPIO_InitStruct.Mode = GPIO_MODE_ANALOG;
    GPIO_InitStruct.Pull = GPIO_NOPULL;
    HAL_GPIO_Init(GPIOE, &GPIO_InitStruct);

    GPIO_InitStruct.Pin = ADC4_11_RJ45_2_Pin;
    GPIO_InitStruct.Mode = GPIO_MODE_ANALOG;
    GPIO_InitStruct.Pull = GPIO_NOPULL;
    HAL_GPIO_Init(ADC4_11_RJ45_2_GPIO_Port, &GPIO_InitStruct);

    /* ADC3 DMA Init */
    /* ADC3 Init */
    hdma_adc3.Instance = DMA2_Channel5;
    hdma_adc3.Init.Direction = DMA_PERIPH_TO_MEMORY;
    hdma_adc3.Init.PeriphInc = DMA_PINC_DISABLE;
    hdma_adc3.Init.MemInc = DMA_MINC_ENABLE;
    hdma_adc3.Init.PeriphDataAlignment = DMA_PDATAALIGN_HALFWORD;
    hdma_adc3.Init.MemDataAlignment = DMA_MDATAALIGN_HALFWORD;
    hdma_adc3.Init.Mode = DMA_CIRCULAR;
    hdma_adc3.Init.Priority = DMA_PRIORITY_HIGH;
    if (HAL_DMA_Init(&hdma_adc3) != HAL_OK)
    {
      _Error_Handler(__FILE__, __LINE__);
    }

    __HAL_LINKDMA(adcHandle,DMA_Handle,hdma_adc3);

    /* ADC3 interrupt Init */
    HAL_NVIC_SetPriority(ADC3_IRQn, 0, 0);
    HAL_NVIC_EnableIRQ(ADC3_IRQn);
  }
  else if(adcHandle->Instance==ADC4)
  {
    /* ADC4 clock enable */
    HAL_RCC_ADC34_CLK_ENABLED++;
    if(HAL_RCC_ADC34_CLK_ENABLED==1){
      __HAL_RCC_ADC34_CLK_ENABLE();
    }
  
    /**ADC4 GPIO Configuration    
    PE15     ------> ADC4_IN2
    PB15     ------> ADC4_IN5
    PD14     ------> ADC4_IN11 
    */
    GPIO_InitStruct.Pin = GPIO_PIN_15;
    GPIO_InitStruct.Mode = GPIO_MODE_ANALOG;
    GPIO_InitStruct.Pull = GPIO_NOPULL;
    HAL_GPIO_Init(GPIOE, &GPIO_InitStruct);

    GPIO_InitStruct.Pin = ADC4_5_RJ45_1_Pin;
    GPIO_InitStruct.Mode = GPIO_MODE_ANALOG;
    GPIO_InitStruct.Pull = GPIO_NOPULL;
    HAL_GPIO_Init(ADC4_5_RJ45_1_GPIO_Port, &GPIO_InitStruct);

    GPIO_InitStruct.Pin = ADC4_11_RJ45_2_Pin;
    GPIO_InitStruct.Mode = GPIO_MODE_ANALOG;
    GPIO_InitStruct.Pull = GPIO_NOPULL;
    HAL_GPIO_Init(ADC4_11_RJ45_2_GPIO_Port, &GPIO_InitStruct);

  }
}

void HAL_ADC_MspDeInit(ADC_HandleTypeDef* adcHandle)
{

  if(adcHandle->Instance==ADC1)
  {
    /* Peripheral clock disable */
    HAL_RCC_ADC12_CLK_ENABLED--;
    if(HAL_RCC_ADC12_CLK_ENABLED==0){
      __HAL_RCC_ADC12_CLK_DISABLE();
    }
  
    /**ADC1 GPIO Configuration    
    PA0     ------> ADC1_IN1 
    */
    HAL_GPIO_DeInit(SINGLEPHASE_GPIO_Port, SINGLEPHASE_Pin);

    /* ADC1 DMA DeInit */
    HAL_DMA_DeInit(adcHandle->DMA_Handle);

    /* ADC1 interrupt Deinit */
  /* USER CODE BEGIN ADC1:ADC1_2_IRQn disable */
    /**
    * Uncomment the line below to disable the "ADC1_2_IRQn" interrupt
    * Be aware, disabling shared interrupt may affect other IPs
    */
    /* HAL_NVIC_DisableIRQ(ADC1_2_IRQn); */
  /* USER CODE END ADC1:ADC1_2_IRQn disable */

  }
  else if(adcHandle->Instance==ADC2)
  {
    /* Peripheral clock disable */
    HAL_RCC_ADC12_CLK_ENABLED--;
    if(HAL_RCC_ADC12_CLK_ENABLED==0){
      __HAL_RCC_ADC12_CLK_DISABLE();
    }
  
    /**ADC2 GPIO Configuration    
    PA5     ------> ADC2_IN2
    PA6     ------> ADC2_IN3
    PA7     ------> ADC2_IN4 
    */
    HAL_GPIO_DeInit(GPIOA, THREEPHASE1_Pin|THREEPHASE2_Pin|THREEPHASE3_Pin);

    /* ADC2 DMA DeInit */
    HAL_DMA_DeInit(adcHandle->DMA_Handle);

    /* ADC2 interrupt Deinit */
  /* USER CODE BEGIN ADC2:ADC1_2_IRQn disable */
    /**
    * Uncomment the line below to disable the "ADC1_2_IRQn" interrupt
    * Be aware, disabling shared interrupt may affect other IPs
    */
    /* HAL_NVIC_DisableIRQ(ADC1_2_IRQn); */
  /* USER CODE END ADC2:ADC1_2_IRQn disable */

  }
  else if(adcHandle->Instance==ADC3)
  {
    /* Peripheral clock disable */
    HAL_RCC_ADC34_CLK_ENABLED--;
    if(HAL_RCC_ADC34_CLK_ENABLED==0){
      __HAL_RCC_ADC34_CLK_DISABLE();
    }
  
    /**ADC3 GPIO Configuration    
    PB0     ------> ADC3_IN12
    PB1     ------> ADC3_IN1
    PE7     ------> ADC3_IN13
    PE8     ------> ADC3_IN6
    PE9     ------> ADC3_IN2
    PE10     ------> ADC3_IN14
    PE11     ------> ADC3_IN15
    PE12     ------> ADC3_IN16
    PE13     ------> ADC3_IN3
    PD14     ------> ADC3_IN11 
    */
    HAL_GPIO_DeInit(GPIOB, GPIO_PIN_0|GPIO_PIN_1);

    HAL_GPIO_DeInit(GPIOE, GPIO_PIN_7|GPIO_PIN_8|GPIO_PIN_9|GPIO_PIN_10 
                          |GPIO_PIN_11|GPIO_PIN_12|GPIO_PIN_13);

    HAL_GPIO_DeInit(ADC4_11_RJ45_2_GPIO_Port, ADC4_11_RJ45_2_Pin);

    /* ADC3 DMA DeInit */
    HAL_DMA_DeInit(adcHandle->DMA_Handle);

    /* ADC3 interrupt Deinit */
    HAL_NVIC_DisableIRQ(ADC3_IRQn);
  }
  else if(adcHandle->Instance==ADC4)
  {
    /* Peripheral clock disable */
    HAL_RCC_ADC34_CLK_ENABLED--;
    if(HAL_RCC_ADC34_CLK_ENABLED==0){
      __HAL_RCC_ADC34_CLK_DISABLE();
    }
  
    /**ADC4 GPIO Configuration    
    PE15     ------> ADC4_IN2
    PB15     ------> ADC4_IN5
    PD14     ------> ADC4_IN11 
    */
    HAL_GPIO_DeInit(GPIOE, GPIO_PIN_15);

    HAL_GPIO_DeInit(ADC4_5_RJ45_1_GPIO_Port, ADC4_5_RJ45_1_Pin);

    HAL_GPIO_DeInit(ADC4_11_RJ45_2_GPIO_Port, ADC4_11_RJ45_2_Pin);

  }
} 

/* USER CODE BEGIN 1 */

void HAL_ADC_ConvHalfCpltCallback(ADC_HandleTypeDef* hadc)
{
  if (hadc==&hadc1) {
    if (conv_hfcplt_flag) adc_buffer_overflow = true; // has the buffer overrun?
    conv_hfcplt_flag = 1;
    
    //process_frame(0);
  }
}

void HAL_ADC_ConvCpltCallback(ADC_HandleTypeDef* hadc)
{
  if (hadc==&hadc1) {
    if (conv_cplt_flag) adc_buffer_overflow = true; // has the buffer overrun?
    conv_cplt_flag = 1;
  }
}


void start_ADCs (int32_t usec_lag) {

  while (!usart_tx_ready); // force wait while usart Tx finishes.
  snprintf(log_buffer, sizeof(log_buffer),
	   "ADC DMA buffs: %d bytes\n", sizeof(adc1_dma_buff));
  debug_printf(log_buffer);
  
  //
  // On the first call they will already be stopped, but in case we're
  // called multiple times to change the usec_lag, make sure they're
  // all stopped.
  //
  HAL_ADC_Stop_DMA(&hadc1);
  HAL_ADC_Stop_DMA(&hadc3);
  
  if (usec_lag == 0) {
    //
    // Caller has requested no lag so set them all to the same edge.
    //
    MODIFY_REG(hadc1.Instance->CFGR, ADC_CFGR_EXTEN, ADC_EXTERNALTRIGCONVEDGE_RISING);
    MODIFY_REG(hadc3.Instance->CFGR, ADC_CFGR_EXTEN, ADC_EXTERNALTRIGCONVEDGE_RISING);
    usec_lag = 1;                                         // any pulse from the timer will do 
    //isr_index = 3;                                        // process ISR when V comes in


  } else if (usec_lag < 0) {
    //
    // Caller wants -ve lag, so Currents on rising, and Voltage on falling.
    //
    MODIFY_REG(hadc1.Instance->CFGR, ADC_CFGR_EXTEN, ADC_EXTERNALTRIGCONVEDGE_RISING);
    MODIFY_REG(hadc3.Instance->CFGR, ADC_CFGR_EXTEN, ADC_EXTERNALTRIGCONVEDGE_FALLING);
    usec_lag = abs(usec_lag);                             // turn it +ve for the timer
    //isr_index = 2;                                        // process ISR when I comes in
  } else {
    //
    // Caller wants a +ve lag, so Currents on falling, and Voltage on rising.
    //
    MODIFY_REG(hadc1.Instance->CFGR, ADC_CFGR_EXTEN, ADC_EXTERNALTRIGCONVEDGE_FALLING);
    MODIFY_REG(hadc3.Instance->CFGR, ADC_CFGR_EXTEN, ADC_EXTERNALTRIGCONVEDGE_RISING);
    //isr_index = 3;                                        // process ISR when V comes in
  }
  if (usec_lag > 9999) usec_lag = 9999;                   // limit of the counter/timer

  
  //
  // These PWM timers in one-shot mode are almost like a pipeline,
  // every action causes the previous action to finally happen.
  // This call stops the last pulse - by generating a pulse with whatever
  // value is set in the GUI and appears above.  We don't want the
  // ADCs to trigger on this one, and it'll take 10 msecs to complete,
  // i.e. the timer will take 10msecs to do it's thing, the call returns
  // immediately, and it makes sure the next pulse will be of the requested
  // duration.
  //
  pulse_tim8_ch2(usec_lag);
  HAL_Delay(100);

  //
  // Now the bogus one has flown through the timer, it's safe to arm the ADCs.
  // After these calls, the next edges on the timer will start them running, forever.
  // The Voltage ADC (ADC4) will start on one edge, all the rest will start on the other.
  // In the case where the caller has requested no timeshift, all four start on the
  // same edge, and the pulse duration makes no difference.
  //
  HAL_ADC_Start_DMA(&hadc1, (uint16_t*)adc1_dma_buff, adc_buff_size);
  HAL_ADC_Start_DMA(&hadc3, (uint16_t*)adc3_dma_buff, adc_buff_size);

  HAL_Delay(100);
  //
  // Now force the last one through (which has the correct settings) and they all
  // kick to life on the appropriate edges.
  //
  pulse_tim8_ch2(usec_lag);
}

/*
void start_ADCs (void) 
{
  // if they're already running.
  HAL_ADC_Stop_DMA(&hadc1);
  HAL_ADC_Stop_DMA(&hadc3);
  //HAL_ADC_Stop_DMA(&hadc4);

  
  pulse_tim8_ch2(usec_lag);


  HAL_Delay(20);
  
  HAL_ADC_Start_DMA(&hadc1, (uint16_t*)adc1_dma_buff, adc_buff_size);
  HAL_ADC_Start_DMA(&hadc3, (uint16_t*)adc3_dma_buff, adc_buff_size);
  //HAL_ADC_Start_DMA(&hadc4, (uint16_t*)adc4_dma_buff, ADC_DMA_BUFFSIZE_PERCHANNEL);
  
  HAL_Delay(100); // this delay is important.

  pulse_tim8_ch2(usec_lag); // trigger, usecs between rising and falling edges.
}
*/
/* USER CODE END 1 */

/**
  * @}
  */

/**
  * @}
  */

/************************ (C) COPYRIGHT STMicroelectronics *****END OF FILE****/
