openenergymonitor/STM32/Software/Sombrero_CB_STM32mini/Src/tim.c

/**
  ******************************************************************************
  * File Name          : TIM.c
  * Description        : This file provides code for the configuration
  *                      of the TIM instances.
  ******************************************************************************
  ** This notice applies to any and all portions of this file
  * that are not between comment pairs USER CODE BEGIN and
  * USER CODE END. Other portions of this file, whether 
  * inserted by the user or by software development tools
  * are owned by their respective copyright owners.
  *
  * COPYRIGHT(c) 2021 STMicroelectronics
  *
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
  ******************************************************************************
  */

/* Includes ------------------------------------------------------------------*/
#include "tim.h"

/* USER CODE BEGIN 0 */

#include "stm32f3xx_ll_tim.h"

/* USER CODE END 0 */

TIM_HandleTypeDef htim8;

/* TIM8 init function */
void MX_TIM8_Init(void)
{
  TIM_MasterConfigTypeDef sMasterConfig;
  TIM_OC_InitTypeDef sConfigOC;
  TIM_BreakDeadTimeConfigTypeDef sBreakDeadTimeConfig;

  htim8.Instance = TIM8;
  htim8.Init.Prescaler = 71;
  htim8.Init.CounterMode = TIM_COUNTERMODE_UP;
  htim8.Init.Period = 9999;
  htim8.Init.ClockDivision = TIM_CLOCKDIVISION_DIV1;
  htim8.Init.RepetitionCounter = 0;
  htim8.Init.AutoReloadPreload = TIM_AUTORELOAD_PRELOAD_DISABLE;
  if (HAL_TIM_PWM_Init(&htim8) != HAL_OK)
  {
    _Error_Handler(__FILE__, __LINE__);
  }

  sMasterConfig.MasterOutputTrigger = TIM_TRGO_RESET;
  sMasterConfig.MasterOutputTrigger2 = TIM_TRGO2_OC2REF;
  sMasterConfig.MasterSlaveMode = TIM_MASTERSLAVEMODE_DISABLE;
  if (HAL_TIMEx_MasterConfigSynchronization(&htim8, &sMasterConfig) != HAL_OK)
  {
    _Error_Handler(__FILE__, __LINE__);
  }

  sConfigOC.OCMode = TIM_OCMODE_PWM1;
  sConfigOC.Pulse = 0;
  sConfigOC.OCPolarity = TIM_OCPOLARITY_HIGH;
  sConfigOC.OCNPolarity = TIM_OCNPOLARITY_HIGH;
  sConfigOC.OCFastMode = TIM_OCFAST_DISABLE;
  sConfigOC.OCIdleState = TIM_OCIDLESTATE_RESET;
  sConfigOC.OCNIdleState = TIM_OCNIDLESTATE_RESET;
  if (HAL_TIM_PWM_ConfigChannel(&htim8, &sConfigOC, TIM_CHANNEL_2) != HAL_OK)
  {
    _Error_Handler(__FILE__, __LINE__);
  }

  sBreakDeadTimeConfig.OffStateRunMode = TIM_OSSR_DISABLE;
  sBreakDeadTimeConfig.OffStateIDLEMode = TIM_OSSI_DISABLE;
  sBreakDeadTimeConfig.LockLevel = TIM_LOCKLEVEL_OFF;
  sBreakDeadTimeConfig.DeadTime = 0;
  sBreakDeadTimeConfig.BreakState = TIM_BREAK_DISABLE;
  sBreakDeadTimeConfig.BreakPolarity = TIM_BREAKPOLARITY_HIGH;
  sBreakDeadTimeConfig.BreakFilter = 0;
  sBreakDeadTimeConfig.Break2State = TIM_BREAK2_DISABLE;
  sBreakDeadTimeConfig.Break2Polarity = TIM_BREAK2POLARITY_HIGH;
  sBreakDeadTimeConfig.Break2Filter = 0;
  sBreakDeadTimeConfig.AutomaticOutput = TIM_AUTOMATICOUTPUT_DISABLE;
  if (HAL_TIMEx_ConfigBreakDeadTime(&htim8, &sBreakDeadTimeConfig) != HAL_OK)
  {
    _Error_Handler(__FILE__, __LINE__);
  }

  HAL_TIM_MspPostInit(&htim8);

}

void HAL_TIM_PWM_MspInit(TIM_HandleTypeDef* tim_pwmHandle)
{

  if(tim_pwmHandle->Instance==TIM8)
  {
    /* TIM8 clock enable */
    __HAL_RCC_TIM8_CLK_ENABLE();
  }
}
void HAL_TIM_MspPostInit(TIM_HandleTypeDef* timHandle)
{

  GPIO_InitTypeDef GPIO_InitStruct;
  if(timHandle->Instance==TIM8)
  {
  
    /**TIM8 GPIO Configuration    
    PA14     ------> TIM8_CH2 
    */
    GPIO_InitStruct.Pin = GPIO_PIN_14;
    GPIO_InitStruct.Mode = GPIO_MODE_AF_PP;
    GPIO_InitStruct.Pull = GPIO_NOPULL;
    GPIO_InitStruct.Speed = GPIO_SPEED_FREQ_LOW;
    GPIO_InitStruct.Alternate = GPIO_AF5_TIM8;
    HAL_GPIO_Init(GPIOA, &GPIO_InitStruct);

  }

}

void HAL_TIM_PWM_MspDeInit(TIM_HandleTypeDef* tim_pwmHandle)
{

  if(tim_pwmHandle->Instance==TIM8)
  {
    /* Peripheral clock disable */
    __HAL_RCC_TIM8_CLK_DISABLE();
  }
} 

/* USER CODE BEGIN 1 */

//
// The timer is configured with /71 pre-scaler to bring it down to 1MHz and
// then a /9999 to give us 10msec total durations (positive+negative).
// PWM output is high for the value set in the h/w register.  We trigger our
// ADCs on the negative pulse, therefore we need to subtract the requested
// pulse duration from 10000 before writing it to the h/w.  A long pulse
// from our caller, means a small positive pulse out of the PWM and a long
// negative pulse.
//
void pulse_tim8_ch2 (int pulse_width_usec) {
  
  HAL_TIM_PWM_Stop(&htim8, TIM_CHANNEL_2);         // In case it's running
  LL_TIM_OC_SetCompareCH2(htim8.Instance, 10000 - pulse_width_usec);
  HAL_TIM_PWM_Start(&htim8, TIM_CHANNEL_2);
  // https://community.openenergymonitor.org/t/stm32-development/6815/53
}



/* USER CODE END 1 */

/**
  * @}
  */

/**
  * @}
  */

/************************ (C) COPYRIGHT STMicroelectronics *****END OF FILE****/
