openenergymonitor/STM32/Software/Sombrero_VE_STM32full_rf69n/Src/rtc.c

/**
  ******************************************************************************
  * File Name          : RTC.c
  * Description        : This file provides code for the configuration
  *                      of the RTC instances.
  ******************************************************************************
  ** This notice applies to any and all portions of this file
  * that are not between comment pairs USER CODE BEGIN and
  * USER CODE END. Other portions of this file, whether 
  * inserted by the user or by software development tools
  * are owned by their respective copyright owners.
  *
  * COPYRIGHT(c) 2020 STMicroelectronics
  *
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
  ******************************************************************************
  */

/* Includes ------------------------------------------------------------------*/
#include "rtc.h"

/* USER CODE BEGIN 0 */
#include <time.h>
/* USER CODE END 0 */

RTC_HandleTypeDef hrtc;

/* RTC init function */
void MX_RTC_Init(void)
{
  RTC_TimeTypeDef sTime;
  RTC_DateTypeDef sDate;

    /**Initialize RTC Only 
    */
  hrtc.Instance = RTC;
  hrtc.Init.HourFormat = RTC_HOURFORMAT_24;
  hrtc.Init.AsynchPrediv = 127;
  hrtc.Init.SynchPrediv = 311;
  hrtc.Init.OutPut = RTC_OUTPUT_DISABLE;
  hrtc.Init.OutPutPolarity = RTC_OUTPUT_POLARITY_HIGH;
  hrtc.Init.OutPutType = RTC_OUTPUT_TYPE_OPENDRAIN;
  if (HAL_RTC_Init(&hrtc) != HAL_OK)
  {
    _Error_Handler(__FILE__, __LINE__);
  }

    /**Initialize RTC and set the Time and Date 
    */
  sTime.Hours = 0x0;
  sTime.Minutes = 0x0;
  sTime.Seconds = 0x0;
  sTime.DayLightSaving = RTC_DAYLIGHTSAVING_NONE;
  sTime.StoreOperation = RTC_STOREOPERATION_RESET;
  if (HAL_RTC_SetTime(&hrtc, &sTime, RTC_FORMAT_BCD) != HAL_OK)
  {
    _Error_Handler(__FILE__, __LINE__);
  }

  sDate.WeekDay = RTC_WEEKDAY_MONDAY;
  sDate.Month = RTC_MONTH_JANUARY;
  sDate.Date = 0x1;
  sDate.Year = 0x0;

  if (HAL_RTC_SetDate(&hrtc, &sDate, RTC_FORMAT_BCD) != HAL_OK)
  {
    _Error_Handler(__FILE__, __LINE__);
  }

}

void HAL_RTC_MspInit(RTC_HandleTypeDef* rtcHandle)
{

  if(rtcHandle->Instance==RTC)
  {
    /* RTC clock enable */
    __HAL_RCC_RTC_ENABLE();
  }
}

void HAL_RTC_MspDeInit(RTC_HandleTypeDef* rtcHandle)
{

  if(rtcHandle->Instance==RTC)
  {
    /* Peripheral clock disable */
    __HAL_RCC_RTC_DISABLE();
  }
} 

/* USER CODE BEGIN 1 */

// The following rtc code from examples folder of F3 firmware package downloaded through CubeMX. (https://www.st.com/en/embedded-software/stm32cubef3.html)
uint8_t aShowTime[50] = {0};
uint8_t aShowDate[50] = {0};
/**
  * @brief  Configure the current time and date, see stm32f3xx_hal_rtc.h.
  * @param  None
  * @retval None
  */
void RTC_CalendarConfig(RTC_DateTypeDef sdatestructure,RTC_TimeTypeDef stimestructure)
{

  /*##-1- Configure the Date #################################################*/
  /* Set Date: Tuesday February 18th 2014 */
  /*
  sdatestructure.Year = 0x14;
  sdatestructure.Month = RTC_MONTH_FEBRUARY; // stm32f3xx_hal_rtc.h
  sdatestructure.Date = 0x18;
  sdatestructure.WeekDay = RTC_WEEKDAY_TUESDAY; //stm32f3xx_hal_rtc.h
  */
  if(HAL_RTC_SetDate(&hrtc,&sdatestructure,RTC_FORMAT_BCD) != HAL_OK)
  {
    /* Initialization Error */
    Error_Handler();
  }

  /*##-2- Configure the Time #################################################*/
  /* Set Time: 02:00:00 */
  /*
  stimestructure.Hours = 0x02;
  stimestructure.Minutes = 0x00;
  stimestructure.Seconds = 0x00;
  stimestructure.TimeFormat = RTC_HOURFORMAT12_AM; // stm32f3xx_hal_rtc.h
  stimestructure.DayLightSaving = RTC_DAYLIGHTSAVING_NONE ;
  stimestructure.StoreOperation = RTC_STOREOPERATION_RESET;
  */
  if (HAL_RTC_SetTime(&hrtc, &stimestructure, RTC_FORMAT_BCD) != HAL_OK)
  {
    /* Initialization Error */
    Error_Handler();
  }

  /*##-3- Writes a data in a RTC Backup data Register1 #######################*/
  //HAL_RTCEx_BKUPWrite(&RtcHandle, RTC_BKP_DR1, 0x32F2);
}

/**
  * @brief  Display the current time and date.
  * @param  showtime : pointer to buffer
  * @param  showdate : pointer to buffer
  * @retval None
  */
void RTC_CalendarShow(uint8_t *showtime, uint8_t *showdate)
{
  RTC_DateTypeDef sdatestructureget;
  RTC_TimeTypeDef stimestructureget;

  /* Get the RTC current Time */
  HAL_RTC_GetTime(&hrtc, &stimestructureget, RTC_FORMAT_BIN);
  /* Get the RTC current Date */
  HAL_RTC_GetDate(&hrtc, &sdatestructureget, RTC_FORMAT_BIN);
  /* Display time Format : hh:mm:ss */
  sprintf((char *)showtime, "Time now is %2d:%2d:%2d", stimestructureget.Hours, stimestructureget.Minutes, stimestructureget.Seconds);
  /* Display date Format : mm-dd-yy */
  sprintf((char *)showdate, "Date today is %2d-%2d-%2d (DD-MM-YY)", sdatestructureget.Date, sdatestructureget.Month, 2000 + sdatestructureget.Year);

}

// helper to convert BCD to decimal https://stackoverflow.com/questions/28133020/how-to-convert-bcd-to-decimal
static int bcd_decimal(uint8_t hex)
{
    //assert(((hex & 0xF0) >> 4) < 10);  // More significant nybble is valid
    //assert((hex & 0x0F) < 10);         // Less significant nybble is valid
    int dec = ((hex & 0xF0) >> 4) * 10 + (hex & 0x0F);
    return dec;
}    
time_t RTC_CalendarShowUnix(void)
{
  // tutorial http://zetcode.com/articles/cdatetime/
  RTC_DateTypeDef sdatestructureget;
  RTC_TimeTypeDef stimestructureget;

  /* Get the RTC current Time */
  HAL_RTC_GetTime(&hrtc, &stimestructureget, RTC_FORMAT_BCD);
  /* Get the RTC current Date */
  HAL_RTC_GetDate(&hrtc, &sdatestructureget, RTC_FORMAT_BCD);
  
  /*
        sdatestructure.Year = uint2bcd(ptm->tm_year-100);
      sdatestructure.Month = uint2bcd(ptm->tm_mon+1);
      sdatestructure.Date = uint2bcd(ptm->tm_mday);
      sdatestructure.WeekDay = uint2bcd(ptm->tm_wday);
      stimestructure.Hours = uint2bcd(ptm->tm_hour);
      stimestructure.Minutes = uint2bcd(ptm->tm_min);
      stimestructure.Seconds = uint2bcd(ptm->tm_sec);
      stimestructure.TimeFormat = RTC_HOURFORMAT12_AM;
      stimestructure.DayLightSaving = RTC_DAYLIGHTSAVING_NONE;
      stimestructure.StoreOperation = RTC_STOREOPERATION_RESET;
      */
  // Pass stm32 time structs to C tm struct.
  //time_t t = time(NULL);
  struct tm tm = {0};
  struct tm *ptm = &tm;
  ptm->tm_sec  = bcd_decimal(stimestructureget.Seconds);
  ptm->tm_min  = bcd_decimal(stimestructureget.Minutes);
  ptm->tm_hour = bcd_decimal(stimestructureget.Hours);
  ptm->tm_wday = bcd_decimal(sdatestructureget.WeekDay);
  ptm->tm_mday = bcd_decimal(sdatestructureget.Date);
  ptm->tm_mon  = bcd_decimal(sdatestructureget.Month) - 1;
  ptm->tm_year = bcd_decimal(sdatestructureget.Year) + 100;
  
  // Create Unix time from tm struct.
  time_t ourtime = mktime(ptm);

  return ourtime;

  /* Display time Format : hh:mm:ss */
  //sprintf((char *)showtime, "Time now is %2d:%2d:%2d", stimestructureget.Hours, stimestructureget.Minutes, stimestructureget.Seconds);
  /* Display date Format : mm-dd-yy */
  //sprintf((char *)showdate, "Date today is %2d-%2d-%2d (DD-MM-YY)", sdatestructureget.Date, sdatestructureget.Month, 2000 + sdatestructureget.Year);

}

/* USER CODE END 1 */

/**
  * @}
  */

/**
  * @}
  */

/************************ (C) COPYRIGHT STMicroelectronics *****END OF FILE****/
