openenergymonitor/STM32/Software/Sombrero_CB_STM32mini/Inc/RFM69.h

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
// Licence can be viewed at
// http://www.gnu.org/licenses/gpl-3.0.txt
//
// Please maintain this license information along with authorship
// and copyright notices in any redistribution of this code
// **********************************************************************************
#ifndef RFM69_h
#define RFM69_h

#include <stdbool.h>
#include <stdint.h>
#include <stdio.h>
#include "usart.h"

uint16_t networkID;
uint8_t nodeID;
uint16_t freqBand;
  /* available frequency bands
  #define RF69_315MHZ            315
  #define RF69_433MHZ            433
  #define RF69_868MHZ            868
  #define RF69_915MHZ            915
  see registers.h for even more.
  */
uint8_t toAddress;
bool requestACK;


#define RF69_MAX_DATA_LEN       61 // to take advantage of the built in AES/CRC we want to limit the frame size to the internal FIFO size (66 bytes - 3 bytes overhead - 2 bytes crc)
#define RF69_SPI_CS             SS // SS is the SPI slave select pin, for instance D10 on ATmega328


#define RF69_IRQ_PIN          2
#define RF69_IRQ_NUM          0


#define CSMA_LIMIT              -90 // upper RX signal sensitivity threshold in dBm for carrier sense access
#define RF69_MODE_SLEEP         0 // XTAL OFF
#define RF69_MODE_STANDBY       1 // XTAL ON
#define RF69_MODE_SYNTH         2 // PLL ON
#define RF69_MODE_RX            3 // RX MODE
#define RF69_MODE_TX            4 // TX MODE

// available frequency bands
#define RF69_315MHZ            315
#define RF69_433MHZ            433
#define RF69_868MHZ            868
#define RF69_915MHZ            915

#define null                  0
#define COURSE_TEMP_COEF    -90 // puts the temperature reading in the ballpark, user can fine tune the returned value
#define RF69_BROADCAST_ADDR 255
#define RF69_CSMA_LIMIT_MS 1000
#define RF69_TX_LIMIT_MS   1000
#define RF69_FSTEP  61.03515625 // == FXOSC / 2^19 = 32MHz / 2^19 (p13 in datasheet)

// TWS: define CTLbyte bits
#define RFM69_CTL_SENDACK   0x80
#define RFM69_CTL_REQACK    0x40

//
#define ISRFM69HW  0

// used function prototypes
bool RFM69_initialize(uint16_t freqBand, uint8_t nodeID, uint16_t networkID);
void RFM69_writeReg(uint8_t addr, uint8_t val);
uint8_t RFM69_readReg(uint8_t addr);
void RFM69_setAddress(uint8_t addr);
void setMode(uint8_t mode);
uint32_t RFM69_getFrequency();
void RFM69_setFrequency(uint32_t freqHz);
void RFM69_setHighPowerRegs(bool onOff);
void RFM69_sleep(void);
void RFM69_setNetwork(uint16_t networkID);
void RFM69_setPowerLevel(uint8_t level); // reduce/increase transmit power level
bool RFM69_canSend(void);
void RFM69_send(uint8_t toAddress, const void* buffer, uint8_t bufferSize, bool requestACK);
bool RFM69_sendWithRetry(uint8_t toAddress, const void* buffer, uint8_t bufferSize, uint8_t retries, uint8_t retryWaitTime); // 40ms roundtrip req for 61byte packets
bool RFM69_ACKReceived(uint8_t fromNodeID);
bool RFM69_receiveDone(void);
bool RFM69_ACKRequested(void);
void RFM69_sendACK(const void* buffer, uint8_t bufferSize);
void RFM69_unselect(void);
void RFM69_interruptHandler(void);
void RFM69_receiveBegin(void);
void RFM69_promiscuous(bool onOff);
void RFM69_readAllRegs(void);
uint8_t RFM69_readTemperature(uint8_t calFactor); // get CMOS temperature (8bit)
void RFM69_rcCalibration(void); // calibrate the internal RC oscillator for use in wide temperature variations - see datasheet section [4.3.5. RC Timer Accuracy]
void RFM69_encrypt(const char* key);
int16_t RFM69_readRSSI(bool forceTrigger);
void RFM69_select(void);
void RFM69_setHighPower(void);
void RFM69_setMode(uint8_t newMode);
void PrintStruct(void);
void PrintByteByByte(void);
void PrintRawBytes(void);

#endif
